OpenARDF/SignalSnagger/Software/AVR128DA48/SignalSnagger/src/eeprommanager.cpp

/*
 *  MIT License
 *
 *  Copyright (c) 2021 DigitalConfections
 *
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
 *  THE SOFTWARE IS PROVIDED "AS IS", WITHOUT WARRANTY OF ANY KIND, EXPRESS OR
 *  IMPLIED, INCLUDING BUT NOT LIMITED TO THE WARRANTIES OF MERCHANTABILITY,
 *  FITNESS FOR A PARTICULAR PURPOSE AND NONINFRINGEMENT. IN NO EVENT SHALL THE
 *  AUTHORS OR COPYRIGHT HOLDERS BE LIABLE FOR ANY CLAIM, DAMAGES OR OTHER
 *  LIABILITY, WHETHER IN AN ACTION OF CONTRACT, TORT OR OTHERWISE, ARISING FROM,
 *  OUT OF OR IN CONNECTION WITH THE SOFTWARE OR THE USE OR OTHER DEALINGS IN THE
 *  SOFTWARE.
 */

#include "defs.h"
#include "eeprommanager.h"
#include "i2c.h"
#include "receiver.h"
#include <avr/pgmspace.h>
#include <string.h>

#ifdef ATMEL_STUDIO_7
#include <avr/pgmspace.h>
#include <stdio.h>
#include <string.h>
#include <math.h>
#endif  /* ATMEL_STUDIO_7 */

/***********************************************************************
 * Global Variables & String Constants
 *
 * Identify each global with a "g_" prefix
 * Whenever possible limit globals' scope to this file using "static"
 * Use "volatile" for globals shared between ISRs and foreground loop
 ************************************************************************/

const struct EE_prom EEMEM EepromManager::ee_vars
=
{
	0x00, // 	uint16_t eeprom_initialization_flag; 
	0x00000000, // 	Guard
	0x00000000, // 	time_t event_start_epoch;
	0x00000000, // 	Guard
	0x00000000, //  time_t event_finish_epoch; 
	0x00000000, // 	Guard
	"\0\0\0\0\0\0\0\0\0\0\0\0\0\0\0\0\0\0\0\0\0", // 	char pattern_text[MAX_PATTERN_TEXT_LENGTH + 2]; 
	0x00000000, // 	Guard
	"\0\0\0\0\0\0\0\0\0\0\0\0\0\0\0\0\0\0\0\0\0", // 	char foxoring_pattern_text[MAX_PATTERN_TEXT_LENGTH + 2];
	0x00000000, // 	Guard
	"\0\0\0\0\0\0\0\0\0\0\0\0\0\0\0\0\0\0\0\0\0",  // char stationID_text[MAX_PATTERN_TEXT_LENGTH + 2];
	0x00000000, // 	Guard
	"\0\0\0\0\0\0\0\0\0", // 	uint8_t unlockCode[MAX_UNLOCK_CODE_LENGTH + 2]; 
	0x00000000, // 	Guard
	(Fox_t)0x00, // Fox_t fox_setting_none;
	0x00000000, // 	Guard
	(Fox_t)0x00, // Fox_t fox_setting_classic;
	0x00000000, // 	Guard
	(Fox_t)0x00, // Fox_t fox_setting_sprint;
	0x00000000, // 	Guard
	(Fox_t)0x00, // Fox_t fox_setting_foxoring;
	0x00000000, // 	Guard
	(Fox_t)0x00, // Fox_t fox_setting_blind;
	0x00000000, // 	Guard
	0x00, // 	uint8_t utc_offset; 
	0x00000000, // 	Guard
	0x00000000, // 	uint32_t rtty_offset; 
	0x00000000, // 	Guard
	0x0000, // 	uint16_t rf_power; 
	0x00000000, // 	Guard
	0x00, // 	uint8_t id_codespeed;
	0x00000000, // 	Guard
	0x00, // 	uint8_t pattern_codespeed;
	0x00000000, // 	Guard
	0x00, // 	uint8_t foxoring_pattern_codespeed;
	0x00000000, // 	Guard
	0x0000, // 	int16_t off_air_seconds; 
	0x00000000, // 	Guard
	0x0000, // 	int16_t on_air_seconds; 
	0x00000000, // 	Guard
	0x0000, // 	int16_t ID_period_seconds; 
	0x00000000, // 	Guard
	0x0000, // 	int16_t intra_cycle_delay_time; 
	0x00000000, // 	Guard
	(Event_t)0x00, // Event_t event_setting;
	0x00000000, // 	Guard
	0x00000000,  // uint32_t frequency;
	0x00000000, // 	Guard
	0x00000000,  // uint32_t frequency_low;
	0x00000000, // 	Guard
	0x00000000,	//	uint32_t frequency_med; 
	0x00000000, // 	Guard
	0x00000000,	// uint32_t frequency_hi;
	0x00000000,	// 	Guard
	0x00000000,	// uint32_t frequency_beacon;
	0x00000000,	// 	Guard
	0x00,		// 	uint8_t master_setting;
	0x00000000, // 	Guard
	0x00000000, //  float voltage_threshold
	0x00000000, // 	Guard
	0x0000,		//  uint16_t clock_calibration
	0x00000000, //  Guard
	0x00,       //  uint8_t days_to_run
	0x00000000, //  Guard
	0x0000,     // uint16_t i2c_failure_count;
	(Frequency_Hz)0x00000000, // Frequency_Memory
	(Frequency_Hz)0x00000000,
	(Frequency_Hz)0x00000000,
	(Frequency_Hz)0x00000000,
	(Frequency_Hz)0x00000000,
	(Frequency_Hz)0x00000000,
	(Frequency_Hz)0x00000000,
	(Frequency_Hz)0x00000000,
	(Frequency_Hz)0x00000000,
	(Frequency_Hz)0x00000000,
	(Frequency_Hz)0x00000000,
	(Frequency_Hz)0x00000000,
	(Frequency_Hz)0x00000000,
	(Frequency_Hz)0x00000000,
	(Frequency_Hz)0x00000000,
	(Frequency_Hz)0x00000000,
	(Frequency_Hz)0x00000000,
	(Frequency_Hz)0x00000000,
	(Frequency_Hz)0x00000000,
	(Frequency_Hz)0x00000000,
	0x00,       //  uint8_t channel name index
	0x00,       //  uint8_t channel name index
	0x00,       //  uint8_t channel name index
	0x00,       //  uint8_t channel name index
	0x00,       //  uint8_t channel name index
	0x00,       //  uint8_t channel name index
	0x00,       //  uint8_t channel name index
	0x00,       //  uint8_t channel name index
	0x00,       //  uint8_t channel name index
	0x00,       //  uint8_t channel name index
	0x00,       //  uint8_t channel name index
	0x00,       //  uint8_t channel name index
	0x00,       //  uint8_t channel name index
	0x00,       //  uint8_t channel name index
	0x00,       //  uint8_t channel name index
	0x00,       //  uint8_t channel name index
	0x00,       //  uint8_t channel name index
	0x00,       //  uint8_t channel name index
	0x00,       //  uint8_t channel name index
	0x00,       //  uint8_t channel name index
	(FrequencyMode_t)0x00,		//  uint8_t frequency_mode
	(BatteryCapacity_t)0x00,       //  uint8_t battery_capacity
	0x00,       //  uint8_t battery_threshold
	0x00		// uint8_t active_memory
};

bool g_isMaster = UNUSED_VAR;
volatile Fox_t g_fox[EVENT_NUMBER_OF_EVENTS] = {FOX_1, FOX_1, SPRINT_S1, FOXORING_FOX1, INVALID_FOX}; /* none, classic, sprint, foxoring, blind */
volatile int8_t g_utc_offset;
uint8_t g_unlockCode[UNLOCK_CODE_SIZE + 2];
Frequency_Hz g_rtty_offset;

volatile Event_t g_event = EVENT_NONE; // unused
extern volatile Frequency_Hz g_rx_frequency;
extern volatile Frequency_Hz g_frequency_low;
extern volatile Frequency_Hz g_frequency_med;
extern volatile Frequency_Hz g_frequency_hi;
extern volatile Frequency_Hz g_frequency_beacon;
extern Frequency_Hz g_channel_frequency[NUMBER_OF_FREQUENCY_CHANNELS];
extern uint8_t g_channel_name[NUMBER_OF_FREQUENCY_CHANNELS];
volatile FrequencyMode_t g_frequency_mode = MODE_VFO;
volatile BatteryCapacity_t g_battery_capacity = MAH_450mAh;
volatile BatteryWarnThreshold_t g_battery_warning_threshold = 10;
volatile uint8_t g_active_memory = 0;

char g_messages_text[STATION_ID+1][MAX_PATTERN_TEXT_LENGTH + 1];
volatile time_t g_event_start_epoch;
volatile time_t g_event_finish_epoch;
uint16_t g_80m_power_level_mW;
volatile uint8_t g_id_codespeed;
volatile uint8_t g_pattern_codespeed;
volatile uint8_t g_foxoring_pattern_codespeed;
volatile int16_t g_off_air_seconds;
volatile int16_t g_on_air_seconds;
volatile int16_t g_ID_period_seconds;
volatile int16_t g_intra_cycle_delay_time;
volatile float g_voltage_threshold = UNUSED_VAR;
extern uint16_t g_clock_calibration;
volatile uint8_t g_days_to_run = UNUSED_VAR;
uint16_t g_i2c_failure_count = UNUSED_VAR;
#define MAX_TX_POWER_80M_MW 5000U
#define EEPROM_RTTY_OFFSET_FREQUENCY_DEFAULT 70
#define EEPROM_TX_80M_POWER_MW_DEFAULT 3000


extern char g_tempStr[];

/* default constructor */
EepromManager::EepromManager()
{
}   /*EepromManager */

/* default destructor */
EepromManager::~EepromManager()
{
}   /*~EepromManager */

#include <inttypes.h>
#include <avr/eeprom.h>
#include <avr/io.h>

typedef uint16_t eeprom_addr_t;

// to write
void avr_eeprom_write_byte(eeprom_addr_t index, uint8_t in) {
	while (NVMCTRL.STATUS & NVMCTRL_EEBUSY_bm);
	_PROTECTED_WRITE_SPM(NVMCTRL.CTRLA, NVMCTRL_CMD_EEERWR_gc);
	*(uint8_t*)(eeprom_addr_t)(MAPPED_EEPROM_START+index) = in;
	_PROTECTED_WRITE_SPM(NVMCTRL.CTRLA, NVMCTRL_CMD_NONE_gc);
}

void avr_eeprom_write_word(eeprom_addr_t index, uint16_t in) {
	while (NVMCTRL.STATUS & NVMCTRL_EEBUSY_bm);
	_PROTECTED_WRITE_SPM(NVMCTRL.CTRLA, NVMCTRL_CMD_EEERWR_gc);
	*(uint16_t*)(eeprom_addr_t)(MAPPED_EEPROM_START+index) = in;
	_PROTECTED_WRITE_SPM(NVMCTRL.CTRLA, NVMCTRL_CMD_NONE_gc);
}

void avr_eeprom_write_dword(eeprom_addr_t index, uint32_t in) {
	while (NVMCTRL.STATUS & NVMCTRL_EEBUSY_bm);
	_PROTECTED_WRITE_SPM(NVMCTRL.CTRLA, NVMCTRL_CMD_EEERWR_gc);
	*(uint32_t*)(eeprom_addr_t)(MAPPED_EEPROM_START+index) = in;
	_PROTECTED_WRITE_SPM(NVMCTRL.CTRLA, NVMCTRL_CMD_NONE_gc);
}

void avr_eeprom_write_float(eeprom_addr_t index, float in) {
	while (NVMCTRL.STATUS & NVMCTRL_EEBUSY_bm);
	_PROTECTED_WRITE_SPM(NVMCTRL.CTRLA, NVMCTRL_CMD_EEERWR_gc);
	*(float*)(eeprom_addr_t)(MAPPED_EEPROM_START+index) = in;
	_PROTECTED_WRITE_SPM(NVMCTRL.CTRLA, NVMCTRL_CMD_NONE_gc);
}


void EepromManager::updateEEPROMVar(EE_var_t v, void* val)
{
	if(!val)
	{
		return;
	}

	switch(v)
	{
		case RTTY_offset:
		{
			if(*(uint32_t*)val != eeprom_read_dword(&(EepromManager::ee_vars.rtty_offset)))
			{
				avr_eeprom_write_dword(RTTY_offset, *(uint32_t*)val);
			}
		}
		break;
		
		case RF_Power:
		{
			if(*(uint16_t*)val != eeprom_read_word(&(EepromManager::ee_vars.rf_power)))
			{
				avr_eeprom_write_word(RF_Power, *(uint16_t*)val);
			}			
		}
		break;
		
		case StationID_text:
		{
			int cnt = 0;
			char* char_addr = (char*)val;
			char c = *char_addr++;
			char q;
			
			eeprom_addr_t j = (eeprom_addr_t)StationID_text;

			while(c && (cnt<MAX_PATTERN_TEXT_LENGTH))
			{
				q = (char)eeprom_read_byte((uint8_t*)j);
				if(c != q)
				{
					avr_eeprom_write_byte(j, c);
				}
				
				cnt++;
				c = *char_addr++;
				j++;
			}

			avr_eeprom_write_byte(j, 0);
		}
		break;

		case Pattern_text:
		{
			int cnt = 0;
			char* char_addr = (char*)val;
			char c = *char_addr++;
			char q;
			
			eeprom_addr_t j = (eeprom_addr_t)Pattern_text;

			while(c && (cnt<MAX_PATTERN_TEXT_LENGTH))
			{
				q = (char)eeprom_read_byte((uint8_t*)j);
				if(c != q)
				{
					avr_eeprom_write_byte(j, c);
				}
				
				cnt++;
				c = *char_addr++;
				j++;
			}

			avr_eeprom_write_byte(j, 0);
		}
		break;
				
		case Foxoring_pattern_text:
		{
			int cnt = 0;
			char* char_addr = (char*)val;
			char c = *char_addr++;
			char q;
			
			eeprom_addr_t j = (eeprom_addr_t)Foxoring_pattern_text;

			while(c && (cnt<MAX_PATTERN_TEXT_LENGTH))
			{
				q = (char)eeprom_read_byte((uint8_t*)j);
				if(c != q)
				{
					avr_eeprom_write_byte(j, c);
				}
				
				cnt++;
				c = *char_addr++;
				j++;
			}

			avr_eeprom_write_byte(j, 0);
		}
		break;

		case UnlockCode:
		{
			int cnt = 0;
			char* char_addr = (char*)val;
			char c = *char_addr++;
			char q;
			
			eeprom_addr_t j = (eeprom_addr_t)UnlockCode;

			while(c && (cnt<MAX_UNLOCK_CODE_LENGTH))
			{
				q = (char)eeprom_read_byte((uint8_t*)j);
				if(c != q)
				{
					avr_eeprom_write_byte(j, c);
				}
				
				cnt++;
				j++;
				c = *char_addr++;
			}

			avr_eeprom_write_byte(j, 0);
		}
		break;

		case Id_codespeed:
		{
			if(*(uint8_t*)val != eeprom_read_byte(&(EepromManager::ee_vars.id_codespeed)))
			{
				avr_eeprom_write_byte(Id_codespeed, *(uint8_t*)val);
			}
		}
		break;
		
		case Pattern_Code_Speed:
		{
			if(*(uint8_t*)val != eeprom_read_byte(&(EepromManager::ee_vars.pattern_codespeed)))
			{
				avr_eeprom_write_byte(Pattern_Code_Speed, *(uint8_t*)val);
			}
		}
		break;
		
		case Foxoring_Pattern_Code_Speed:
		{
			if(*(uint8_t*)val != eeprom_read_byte(&(EepromManager::ee_vars.foxoring_pattern_codespeed)))
			{
				avr_eeprom_write_byte(Foxoring_Pattern_Code_Speed, *(uint8_t*)val);
			}
		}
		break;

		case Fox_setting_none:
		{
			if(*(uint8_t*)val != eeprom_read_byte((uint8_t*)&(EepromManager::ee_vars.fox_setting_none)))
			{
				avr_eeprom_write_byte(Fox_setting_none, *(uint8_t*)val);
			}
		}
		break;
		
		case Fox_setting_classic:
		{
			if(*(uint8_t*)val != eeprom_read_byte((uint8_t*)&(EepromManager::ee_vars.fox_setting_classic)))
			{
				avr_eeprom_write_byte(Fox_setting_classic, *(uint8_t*)val);
			}
		}
		break;
		
		case Fox_setting_sprint:
		{
			if(*(uint8_t*)val != eeprom_read_byte((uint8_t*)&(EepromManager::ee_vars.fox_setting_sprint)))
			{
				avr_eeprom_write_byte(Fox_setting_sprint, *(uint8_t*)val);
			}
		}
		break;
		
		case Fox_setting_foxoring:
		{
			if(*(uint8_t*)val != eeprom_read_byte((uint8_t*)&(EepromManager::ee_vars.fox_setting_foxoring)))
			{
				avr_eeprom_write_byte(Fox_setting_foxoring, *(uint8_t*)val);
			}
		}
		break;
		
		case Fox_setting_blind:
		{
			if(*(uint8_t*)val != eeprom_read_byte((uint8_t*)&(EepromManager::ee_vars.fox_setting_blind)))
			{
				avr_eeprom_write_byte(Fox_setting_blind, *(uint8_t*)val);
			}			
		}
		break;
		
		case Master_setting:
		{
			if(*(uint8_t*)val != eeprom_read_byte((uint8_t*)&(EepromManager::ee_vars.master_setting)))
			{
				avr_eeprom_write_byte(Master_setting, *(uint8_t*)val);
			}
		}
		break;
		
		case Event_setting:
		{
			if(*(uint8_t*)val != eeprom_read_byte((uint8_t*)&(EepromManager::ee_vars.event_setting)))
			{
				avr_eeprom_write_byte(Event_setting, *(uint8_t*)val);
			}
		}
		break;
		
		case Frequency:
		{
			if(*(uint32_t*)val != eeprom_read_dword(&(EepromManager::ee_vars.frequency)))
			{
				avr_eeprom_write_dword(Frequency, *(uint32_t*)val);
			}
		}
		break;
		
		case Frequency_Low:
		{
			if(*(uint32_t*)val != eeprom_read_dword(&(EepromManager::ee_vars.frequency_low)))
			{
				avr_eeprom_write_dword(Frequency_Low, *(uint32_t*)val);
			}
		}
		break;
		
		case Frequency_Med:
		{
			if(*(uint32_t*)val != eeprom_read_dword(&(EepromManager::ee_vars.frequency_med)))
			{
				avr_eeprom_write_dword(Frequency_Med, *(uint32_t*)val);
			}
		}
		break;
		
		case Frequency_Hi:
		{
			if(*(uint32_t*)val != eeprom_read_dword(&(EepromManager::ee_vars.frequency_high)))
			{
				avr_eeprom_write_dword(Frequency_Hi, *(uint32_t*)val);
			}
		}
		break;
		
		case Frequency_Beacon:
		{
			if(*(uint32_t*)val != eeprom_read_dword(&(EepromManager::ee_vars.frequency_beacon)))
			{
				avr_eeprom_write_dword(Frequency_Beacon, *(uint32_t*)val);
			}
		}
		break;

		case Event_start_epoch:
		{
			if(*(uint32_t*)val != eeprom_read_dword(&(EepromManager::ee_vars.event_start_epoch)))
			{
				avr_eeprom_write_dword(Event_start_epoch, *(uint32_t*)val);
			}
		}
		break;

		case Event_finish_epoch:
		{
			if(*(uint32_t*)val != eeprom_read_dword(&(EepromManager::ee_vars.event_finish_epoch)))
			{
				avr_eeprom_write_dword(Event_finish_epoch, *(uint32_t*)val);
			}		
		}
		break;

		case Utc_offset:
		{
			if(*(uint8_t*)val != eeprom_read_byte(&(EepromManager::ee_vars.utc_offset)))
			{
				avr_eeprom_write_byte(Utc_offset, *(uint8_t*)val);
			}		
		}
		break;
		
		case Off_Air_Seconds:
		{
			if(*(int16_t*)val != (int16_t)eeprom_read_word((const uint16_t *)&(EepromManager::ee_vars.off_air_seconds)))
			{
				avr_eeprom_write_word(Off_Air_Seconds, *(uint16_t*)val);
			}
		}
		break;
		
		case On_Air_Seconds:
		{
			if(*(int16_t*)val != (int16_t)eeprom_read_word((const uint16_t *)&(EepromManager::ee_vars.on_air_seconds)))
			{
				avr_eeprom_write_word(On_Air_Seconds, *(uint16_t*)val);
			}
		}
		break;
		
		case ID_Period_Seconds:
		{
			if(*(int16_t*)val != (int16_t)eeprom_read_word((const uint16_t *)&(EepromManager::ee_vars.ID_period_seconds)))
			{
				avr_eeprom_write_word(ID_Period_Seconds, *(uint16_t*)val);
			}
		}
		break;
		
		case Intra_Cycle_Delay_Seconds:
		{
			if(*(int16_t*)val != (int16_t)eeprom_read_word((const uint16_t *)&(EepromManager::ee_vars.intra_cycle_delay_time)))
			{
				avr_eeprom_write_word(Intra_Cycle_Delay_Seconds, *(uint16_t*)val);
			}		
		}
		break;

		case Eeprom_initialization_flag:
		{
			if(*(int16_t*)val != (int16_t)eeprom_read_word((const uint16_t *)&(EepromManager::ee_vars.eeprom_initialization_flag)))
			{
				avr_eeprom_write_word(Eeprom_initialization_flag, *(uint16_t*)val);
			}		
		}
		break;
		
		case Voltage_threshold:
		{
			if(*(float*)val != eeprom_read_float(&(EepromManager::ee_vars.voltage_threshold)))
			{
				avr_eeprom_write_float(Voltage_threshold, *(float*)val);
			}
		}
		break;
		
		case Clock_calibration:
		{
			if(*(uint16_t*)val != eeprom_read_word(&(EepromManager::ee_vars.clock_calibration)))
			{
				avr_eeprom_write_word(Clock_calibration, *(uint16_t*)val);
			}
		}
		break;
		
		
		case Days_to_run:
		{
			if(*(uint8_t*)val != eeprom_read_byte(&(EepromManager::ee_vars.days_to_run)))
			{
				avr_eeprom_write_byte(Days_to_run, *(uint8_t*)val);
			}
		}
		break;
		
		
		case I2C_failure_count:
		{
			if(*(uint16_t*)val != eeprom_read_word(&(EepromManager::ee_vars.i2c_failure_count)))
			{
				avr_eeprom_write_byte(I2C_failure_count, *(uint8_t*)val);
			}
		}
		break;
		
		
		case Frequency_Memory:
		{
			int cnt = 0;
			Frequency_Hz* freq_addr = (Frequency_Hz*)val;
			Frequency_Hz f = *freq_addr;
			Frequency_Hz q;
			
			eeprom_addr_t j = (eeprom_addr_t)Frequency_Memory;

			while(cnt<NUMBER_OF_FREQUENCY_CHANNELS)
			{
				q = (Frequency_Hz)eeprom_read_dword((uint32_t*)j);
				if(f != q)
				{
					avr_eeprom_write_dword(j, f);
				}

				cnt++;
				freq_addr++;
				f = *freq_addr;
				j += 4;
			}
		}
		break;
		
		
		case Channel_Name:
		{
			int cnt = 0;
			uint8_t* name_addr = (uint8_t*)val;
			uint8_t n = *name_addr;
			uint8_t q;
			
			eeprom_addr_t j = (eeprom_addr_t)Channel_Name;

			while(cnt<NUMBER_OF_FREQUENCY_CHANNELS)
			{
				q = (uint8_t)eeprom_read_byte((uint8_t*)j);
				if(n != q)
				{
					avr_eeprom_write_dword(j, n);
				}

				cnt++;
				name_addr++;
				n = *name_addr;
				j++;
			}
		}
		break;
		
		
		case Frequency_Mode:
		{
			if(*(uint8_t*)val != eeprom_read_byte((uint8_t*)&(EepromManager::ee_vars.frequency_mode)))
			{
				avr_eeprom_write_byte(Frequency_Mode, *(uint8_t*)val);
			}
		}
		break;
		
		
		case Battery_Capacity:
		{
			if(*(uint8_t*)val != eeprom_read_byte((uint8_t*)&(EepromManager::ee_vars.battery_capacity)))
			{
				avr_eeprom_write_byte(Battery_Capacity, *(uint8_t*)val);
			}
		}
		break;
		
		
		case Battery_Threshold:
		{
			if(*(uint8_t*)val != eeprom_read_byte((uint8_t*)&(EepromManager::ee_vars.battery_threshold)))
			{
				avr_eeprom_write_byte(Battery_Threshold, *(uint8_t*)val);
			}
		}
		break;
		
		
		case Active_Memory:
		{
			if(*(uint8_t*)val != eeprom_read_byte((uint8_t*)&(EepromManager::ee_vars.active_memory)))
			{
				avr_eeprom_write_byte(Active_Memory, *(uint8_t*)val);
			}
		}
		break;

		default:
		{

		}
		break;
	}
}

/** 
 * Store any changed EEPROM variables
 */
void EepromManager::saveAllEEPROM(void)
{
	updateEEPROMVar(Id_codespeed, (void*)&g_id_codespeed);	
	updateEEPROMVar(Fox_setting_none, (void*)&g_fox[EVENT_NONE]);
	updateEEPROMVar(Fox_setting_classic, (void*)&g_fox[EVENT_CLASSIC]);
	updateEEPROMVar(Fox_setting_sprint, (void*)&g_fox[EVENT_SPRINT]);
	updateEEPROMVar(Fox_setting_foxoring, (void*)&g_fox[EVENT_FOXORING]);
	updateEEPROMVar(Fox_setting_blind, (void*)&g_fox[EVENT_BLIND_ARDF]);
	updateEEPROMVar(Event_setting, (void*)&g_event);
	updateEEPROMVar(Frequency, (void*)&g_rx_frequency);
	updateEEPROMVar(Frequency_Low, (void*)&g_frequency_low);
	updateEEPROMVar(Frequency_Med, (void*)&g_frequency_med); /* use for sprint slow */
	updateEEPROMVar(Frequency_Hi, (void*)&g_frequency_hi); /* use for sprint high - will also need sprint spectator and beacon */
	updateEEPROMVar(Frequency_Beacon, (void*)&g_frequency_beacon);
	updateEEPROMVar(Event_start_epoch, (void*)&g_event_start_epoch);
	updateEEPROMVar(Event_finish_epoch, (void*)&g_event_finish_epoch);
	updateEEPROMVar(Utc_offset, (void*)&g_utc_offset);
	updateEEPROMVar(Pattern_text, (void*)g_messages_text[PATTERN_TEXT]);
	updateEEPROMVar(Foxoring_pattern_text, (void*)g_messages_text[FOXORING_PATTERN_TEXT]);
	updateEEPROMVar(StationID_text, (void*)g_messages_text[STATION_ID]);
	updateEEPROMVar(UnlockCode, (void*)g_unlockCode);
	updateEEPROMVar(RTTY_offset, (void*)&g_rtty_offset);
	updateEEPROMVar(RF_Power, (void*)&g_80m_power_level_mW);
	updateEEPROMVar(Pattern_Code_Speed, (void*)&g_pattern_codespeed);
	updateEEPROMVar(Foxoring_Pattern_Code_Speed, (void*)&g_foxoring_pattern_codespeed);
	updateEEPROMVar(Off_Air_Seconds, (void*)&g_off_air_seconds);
	updateEEPROMVar(On_Air_Seconds, (void*)&g_on_air_seconds);
	updateEEPROMVar(ID_Period_Seconds, (void*)&g_ID_period_seconds);
	updateEEPROMVar(Intra_Cycle_Delay_Seconds, (void*)&g_intra_cycle_delay_time);
	updateEEPROMVar(Voltage_threshold, (void*)&g_voltage_threshold);
	updateEEPROMVar(Clock_calibration, (void*)&g_clock_calibration);
	updateEEPROMVar(Days_to_run, (void*)&g_days_to_run);
	updateEEPROMVar(I2C_failure_count, (void*)&g_i2c_failure_count);
	updateEEPROMVar(Frequency_Memory, (void*)&g_channel_frequency[0]);
	updateEEPROMVar(Channel_Name, (void*)&g_channel_name[0]);
	updateEEPROMVar(Frequency_Mode, (void*)&g_frequency_mode);
	updateEEPROMVar(Battery_Capacity, (void*)&g_battery_capacity);
	updateEEPROMVar(Battery_Threshold, (void*)&g_battery_warning_threshold);
	updateEEPROMVar(Active_Memory, (void*)&g_active_memory);
}


bool EepromManager::readNonVols(void)
{
	bool failure = true;
	uint16_t i;
	uint16_t initialization_flag = eeprom_read_word(0);

	if(initialization_flag == EEPROM_INITIALIZED_FLAG)  /* EEPROM is up to date */
	{
		g_isMaster = EEPROM_MASTER_SETTING_DEFAULT; // (int8_t)eeprom_read_byte(&(EepromManager::ee_vars.master_setting));
		g_id_codespeed = CLAMP(MIN_CODE_SPEED_WPM, eeprom_read_byte(&(EepromManager::ee_vars.id_codespeed)), MAX_CODE_SPEED_WPM);
		g_event = (Event_t)eeprom_read_byte((const uint8_t*)&(EepromManager::ee_vars.event_setting));
		g_rx_frequency = CLAMP(RX_MINIMUM_80M_FREQUENCY, eeprom_read_dword(&(EepromManager::ee_vars.frequency)), RX_MAXIMUM_80M_FREQUENCY);
		g_frequency_low = CLAMP(RX_MINIMUM_80M_FREQUENCY, eeprom_read_dword(&(EepromManager::ee_vars.frequency_low)), RX_MAXIMUM_80M_FREQUENCY);
		g_frequency_med = CLAMP(RX_MINIMUM_80M_FREQUENCY, eeprom_read_dword(&(EepromManager::ee_vars.frequency_med)), RX_MAXIMUM_80M_FREQUENCY);
		g_frequency_hi = CLAMP(RX_MINIMUM_80M_FREQUENCY, eeprom_read_dword(&(EepromManager::ee_vars.frequency_high)), RX_MAXIMUM_80M_FREQUENCY);
		g_frequency_beacon = CLAMP(RX_MINIMUM_80M_FREQUENCY, eeprom_read_dword(&(EepromManager::ee_vars.frequency_beacon)), RX_MAXIMUM_80M_FREQUENCY);
		g_fox[EVENT_NONE] = (Fox_t)(CLAMP(BEACON, eeprom_read_byte((uint8_t*)&(EepromManager::ee_vars.fox_setting_none)), SPRINT_F5));
		g_fox[EVENT_CLASSIC] = (Fox_t)(CLAMP(BEACON, eeprom_read_byte((uint8_t*)&(EepromManager::ee_vars.fox_setting_classic)), FOX_5));
		g_fox[EVENT_SPRINT] = (Fox_t)(CLAMP(BEACON, eeprom_read_byte((uint8_t*)&(EepromManager::ee_vars.fox_setting_sprint)), SPRINT_F5));
		g_fox[EVENT_FOXORING] = (Fox_t)(CLAMP(BEACON, eeprom_read_byte((uint8_t*)&(EepromManager::ee_vars.fox_setting_foxoring)), FOXORING_FOX3));
		g_fox[EVENT_BLIND_ARDF] = (Fox_t)(CLAMP(BEACON, eeprom_read_byte((uint8_t*)&(EepromManager::ee_vars.fox_setting_blind)), FOX_5));
		g_event_start_epoch = eeprom_read_dword(&(EepromManager::ee_vars.event_start_epoch));
		g_event_finish_epoch = eeprom_read_dword(&(EepromManager::ee_vars.event_finish_epoch));
		g_utc_offset = (int8_t)eeprom_read_byte(&(EepromManager::ee_vars.utc_offset));

		char c;
		for(i = 0; i < MAX_PATTERN_TEXT_LENGTH; i++)
		{
			c = (char)eeprom_read_byte((uint8_t*)(&(EepromManager::ee_vars.pattern_text[i])));			
			if(c==255) c=0;
			g_messages_text[PATTERN_TEXT][i] = c;
			if(!c)
			{
				break;
			}
		}

		for(i = 0; i < MAX_PATTERN_TEXT_LENGTH; i++)
		{
			c = (char)eeprom_read_byte((uint8_t*)(&(EepromManager::ee_vars.foxoring_pattern_text[i])));			
			if(c==255) c=0;
			g_messages_text[FOXORING_PATTERN_TEXT][i] = c;
			if(!c)
			{
				break;
			}
		}

		for(i = 0; i < MAX_PATTERN_TEXT_LENGTH; i++)
		{
			c = (char)eeprom_read_byte((uint8_t*)(&(EepromManager::ee_vars.stationID_text[i])));
			if(c == 255) c= 0;
			g_messages_text[STATION_ID][i] = c;
			if(!c)
			{
				break;
			}
		}

		for(i = 0; i < MAX_UNLOCK_CODE_LENGTH; i++)
		{
			c = (char)eeprom_read_byte((uint8_t*)(&(EepromManager::ee_vars.unlockCode[i])));	
			if(c==255) c=0;
			g_unlockCode[i] = c;
			if(!c)
			{
				break;
			}
		}
		
		g_rtty_offset =eeprom_read_dword(&(EepromManager::ee_vars.rtty_offset));
 		g_80m_power_level_mW = CLAMP(MIN_RF_POWER_MW, (uint16_t)eeprom_read_word(&(EepromManager::ee_vars.rf_power)), MAX_TX_POWER_80M_MW);

		g_pattern_codespeed = CLAMP(MIN_CODE_SPEED_WPM, eeprom_read_byte((uint8_t*)(&(EepromManager::ee_vars.pattern_codespeed))), MAX_CODE_SPEED_WPM);
		g_foxoring_pattern_codespeed = CLAMP(MIN_CODE_SPEED_WPM, eeprom_read_byte((uint8_t*)(&(EepromManager::ee_vars.foxoring_pattern_codespeed))), MAX_CODE_SPEED_WPM);

		g_off_air_seconds = CLAMP(0, (int16_t)eeprom_read_word((const uint16_t*)&(EepromManager::ee_vars.off_air_seconds)), 3600);
		g_on_air_seconds = CLAMP(0, (int16_t)eeprom_read_word((const uint16_t*)&(EepromManager::ee_vars.on_air_seconds)), 3600);
		g_ID_period_seconds = CLAMP(0, (int16_t)eeprom_read_word((const uint16_t*)&(EepromManager::ee_vars.ID_period_seconds)), 3600);
		g_intra_cycle_delay_time = CLAMP(0, (int16_t)eeprom_read_word((const uint16_t*)&(EepromManager::ee_vars.intra_cycle_delay_time)), 3600);
		
		g_voltage_threshold = CLAMP(0.1, eeprom_read_float(&(EepromManager::ee_vars.voltage_threshold)), 15.0);
		
		g_clock_calibration = eeprom_read_word(&(EepromManager::ee_vars.clock_calibration));

		g_days_to_run = eeprom_read_byte((uint8_t*)(&(EepromManager::ee_vars.days_to_run)));
		
		g_i2c_failure_count = eeprom_read_word((uint16_t*)(&(EepromManager::ee_vars.i2c_failure_count)));
		
		Frequency_Hz f;
		for(i = 0; i < NUMBER_OF_FREQUENCY_CHANNELS; i++)
		{
			f = eeprom_read_dword(&(EepromManager::ee_vars.channel_frequency[i]));
			if(f==0xFFFFFFFF) f=0;
			if((f==0) || ((f <= RX_MAXIMUM_80M_FREQUENCY) && (f >= RX_MINIMUM_80M_FREQUENCY)))
			{
				g_channel_frequency[i] = f;
			}
		}
		
		uint8_t x;
		for(i=0; i<NUMBER_OF_FREQUENCY_CHANNELS; i++)
		{
			x = eeprom_read_byte(&(EepromManager::ee_vars.channel_name[i]));
			if(x >= NUMBER_OF_FREQUENCY_CHANNEL_NAMES) x = 0;
			g_channel_name[i] = x;
		}
		
		g_frequency_mode = (FrequencyMode_t)eeprom_read_byte((const uint8_t*)&(EepromManager::ee_vars.frequency_mode));
		if(g_frequency_mode != MODE_MEMORY) g_frequency_mode = MODE_VFO;
		
		g_battery_capacity = (BatteryCapacity_t)eeprom_read_byte((uint8_t*)&(EepromManager::ee_vars.battery_capacity));
		if((uint8_t)g_battery_capacity > NUMBER_OF_BATTERY_CAPACITY_VALUES) g_battery_capacity = MAH_450mAh;
		
		g_battery_warning_threshold = (BatteryWarnThreshold_t)eeprom_read_byte((uint8_t*)&(EepromManager::ee_vars.battery_threshold));
		if((uint8_t)g_battery_warning_threshold > 100) g_battery_warning_threshold = 10;
		
		g_active_memory = (uint8_t)eeprom_read_byte((uint8_t*)&(EepromManager::ee_vars.active_memory));
		if((uint8_t)g_active_memory > NUMBER_OF_FREQUENCY_CHANNELS) g_active_memory = 0;

		failure = false;
	}

	return(failure);
}

/*
 * Set volatile variables to their values stored in EEPROM
 */
	bool EepromManager::initializeEEPROMVars(void)
	{
		bool err = false;
		uint16_t i, j;

		uint16_t initialization_flag = eeprom_read_word(0);

		if(initialization_flag != EEPROM_INITIALIZED_FLAG)
		{
			g_id_codespeed = EEPROM_ID_CODE_SPEED_DEFAULT;
			avr_eeprom_write_byte(Id_codespeed, g_id_codespeed);
			
			g_isMaster = EEPROM_MASTER_SETTING_DEFAULT;
			avr_eeprom_write_byte(Master_setting, g_isMaster);

			g_fox[EVENT_NONE] = EEPROM_FOX_SETTING_NONE_DEFAULT;
			avr_eeprom_write_byte(Fox_setting_none, (uint8_t)g_fox[EVENT_NONE]);
			
			g_fox[EVENT_CLASSIC] = EEPROM_FOX_SETTING_CLASSIC_DEFAULT;
			avr_eeprom_write_byte(Fox_setting_classic, (uint8_t)g_fox[EVENT_CLASSIC]);
			
			g_fox[EVENT_SPRINT] = EEPROM_FOX_SETTING_SPRINT_DEFAULT;
			avr_eeprom_write_byte(Fox_setting_sprint, (uint8_t)g_fox[EVENT_SPRINT]);
			
			g_fox[EVENT_FOXORING] = EEPROM_FOX_SETTING_FOXORING_DEFAULT;
			avr_eeprom_write_byte(Fox_setting_foxoring, (uint8_t)g_fox[EVENT_FOXORING]);
			
			g_fox[EVENT_BLIND_ARDF] = EEPROM_FOX_SETTING_BLIND_DEFAULT;
			avr_eeprom_write_byte(Fox_setting_blind, (uint8_t)g_fox[EVENT_BLIND_ARDF]);
			
			g_event = EEPROM_EVENT_SETTING_DEFAULT;
			avr_eeprom_write_byte(Event_setting, (uint8_t)g_event);
			
			g_rx_frequency = EEPROM_FREQUENCY_DEFAULT;
			avr_eeprom_write_dword(Frequency, g_rx_frequency);
			
			g_frequency_low = EEPROM_FREQUENCY_LOW_DEFAULT;
			avr_eeprom_write_dword(Frequency_Low, g_frequency_low);
			
			g_frequency_med = EEPROM_FREQUENCY_MED_DEFAULT;
			avr_eeprom_write_dword(Frequency_Med, g_frequency_med);
			
			g_frequency_hi = EEPROM_FREQUENCY_HI_DEFAULT;
			avr_eeprom_write_dword(Frequency_Hi, g_frequency_hi);
			
			g_frequency_beacon = EEPROM_FREQUENCY_BEACON_DEFAULT;
			avr_eeprom_write_dword(Frequency_Beacon, g_frequency_beacon);

			g_event_start_epoch = EEPROM_START_EPOCH_DEFAULT;
			avr_eeprom_write_dword(Event_start_epoch, g_event_start_epoch);

			g_event_finish_epoch = EEPROM_FINISH_EPOCH_DEFAULT;
			avr_eeprom_write_dword(Event_finish_epoch, g_event_finish_epoch);

			g_utc_offset = EEPROM_UTC_OFFSET_DEFAULT;
			avr_eeprom_write_byte(Utc_offset, (uint8_t)g_utc_offset);

			g_messages_text[STATION_ID][0] = '\0';
			avr_eeprom_write_byte(StationID_text, 0);

			uint8_t *v = (uint8_t*)EEPROM_FOX_PATTERN_DEFAULT;
			i = Pattern_text;
			for(j = 0; j < strlen(EEPROM_FOX_PATTERN_DEFAULT); j++)
			{
				g_messages_text[PATTERN_TEXT][j] = *v;
				avr_eeprom_write_byte(i++, *v++);
			}
			
			avr_eeprom_write_byte(i, '\0');

			v = (uint8_t*)EEPROM_FOXORING_PATTERN_DEFAULT;
			i = Foxoring_pattern_text;
			for(j = 0; j < strlen(EEPROM_FOXORING_PATTERN_DEFAULT); j++)
			{
				g_messages_text[FOXORING_PATTERN_TEXT][j] = *v;
				avr_eeprom_write_byte(i++, *v++);
			}
			
			avr_eeprom_write_byte(i, '\0');

			v = (uint8_t*)EEPROM_DTMF_UNLOCK_CODE_DEFAULT;
			i = UnlockCode;
			for(j = 0; j < strlen(EEPROM_DTMF_UNLOCK_CODE_DEFAULT); j++)
			{
				g_unlockCode[j] = *v;
				avr_eeprom_write_byte(i++, *v++);
			}

			avr_eeprom_write_byte(i, '\0');
			g_unlockCode[j] = '\0';
			
			g_rtty_offset = EEPROM_RTTY_OFFSET_FREQUENCY_DEFAULT;
			avr_eeprom_write_dword(RTTY_offset, g_rtty_offset);

			g_80m_power_level_mW = EEPROM_TX_80M_POWER_MW_DEFAULT;
			avr_eeprom_write_dword(RF_Power, g_80m_power_level_mW);
			
			g_pattern_codespeed = EEPROM_PATTERN_CODE_SPEED_DEFAULT;
			avr_eeprom_write_byte(Pattern_Code_Speed, g_pattern_codespeed);
			
			g_foxoring_pattern_codespeed = EEPROM_FOXORING_PATTERN_CODESPEED_DEFAULT;
			avr_eeprom_write_byte(Foxoring_Pattern_Code_Speed, g_foxoring_pattern_codespeed);
			
			g_off_air_seconds = EEPROM_OFF_AIR_TIME_DEFAULT;
			avr_eeprom_write_word(Off_Air_Seconds, g_off_air_seconds);
			
			g_on_air_seconds = EEPROM_ON_AIR_TIME_DEFAULT;
			avr_eeprom_write_word(On_Air_Seconds, g_on_air_seconds);
		
			g_ID_period_seconds = EEPROM_ID_TIME_INTERVAL_DEFAULT;
			avr_eeprom_write_word(ID_Period_Seconds, g_ID_period_seconds);
			
			g_intra_cycle_delay_time = EEPROM_INTRA_CYCLE_DELAY_TIME_DEFAULT;
			avr_eeprom_write_word(Intra_Cycle_Delay_Seconds, g_intra_cycle_delay_time);

			avr_eeprom_write_byte(i, '\0');

			g_voltage_threshold = EEPROM_BATTERY_THRESHOLD_V;
			avr_eeprom_write_float(Voltage_threshold, g_voltage_threshold);
			
			g_clock_calibration = EEPROM_CLOCK_CALIBRATION_DEFAULT;
			avr_eeprom_write_word(Clock_calibration, g_clock_calibration);

			g_days_to_run = 1;
			avr_eeprom_write_byte(Days_to_run, g_days_to_run);
			
			g_i2c_failure_count = 0;
			avr_eeprom_write_dword(I2C_failure_count, g_i2c_failure_count);

			i = Frequency_Memory;
			for(j = 0; j < NUMBER_OF_FREQUENCY_CHANNELS; j++)
			{
				g_channel_frequency[j] = 0;
				avr_eeprom_write_dword(i, 0);
				i += 4;
			}
			
			i = Channel_Name;
			for(j=0; j<NUMBER_OF_FREQUENCY_CHANNELS; j++)
			{
				g_channel_name[j] = 0;
				avr_eeprom_write_byte(i++, 0);
			}
			
			g_frequency_mode = MODE_VFO;
			avr_eeprom_write_byte(Frequency_Mode, g_frequency_mode);
			
			g_battery_capacity = MAH_450mAh;
			avr_eeprom_write_byte(Battery_Capacity, g_battery_capacity);
			
			g_battery_warning_threshold = 10;
			avr_eeprom_write_byte(Battery_Threshold, g_battery_warning_threshold);
			
			/* Done */

			avr_eeprom_write_word(0, EEPROM_INITIALIZED_FLAG);
		}
		
		return(err);
	}
