OpenARDF/SignalSnagger/Software/AVR128DA48/SignalSnagger/include/si5351.h

/*
 *  MIT License
 *
 *  Copyright (c) 2022 DigitalConfections
 *
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
 * The Si5351 is an I2C configurable clock generator that is ideally suited for replacing crystals,
 * crystal oscillators, VCXOs, phase-locked loops (PLLs), and fanout buffers in cost-sensitive
 * applications. Based on a PLL/VCXO + high resolution MultiSynth fractional divider architecture,
 * the Si5351 can generate any frequency up to 200 MHz on each of its outputs with 0 ppm error.
 * http://www.silabs.com/documents/public/data-sheets/Si5351-B.pdf
 *
 * PURPOSE
 * This is a basic library for the Si5351 series of clock generator ICs from Silicon Labs for the avr-gcc development
 * environment. It supports controlling the Si5351 with an AVR microcontroller with a TWI peripheral module. It is
 * intentionally minimalistic in order to minimize program size and maximize execution speed. It is intended for use
 * in projects utilizing small processors with limited program memory, where the program author is responsible for
 * implementing any checks on the validity of parameters passed to the library functions.
 *
 * The following high-level description of the Si5351 frequency-setting algorithm is provided to help the user understand
 * the basic workings of the library, so that any needed modifications can be readily made.
 *
 * OVERVIEW
 * The algorithm used in this library starts with the desired output frequency, and works backwards through Synthesis
 * Stage 2 and Synthesis Stage 1, to determine the necessary Si5351 register settings.
 *
 * STEPS (Output CLK0)
 *
 * 1. Choose a desired CLK0 output frequency (Fout) in Hz.
 * 2. Find an even integer Multisynth Divider Ratio (a_msd) that multiplies Fout to obtain a value between 600 MHz and 900 MHz. Set b_msd = 0,
 *    and c_msd = 1. Note: a_msd has a valid range of all even integers between 4 and 900; we are choosing to exclude all odd and fractional solutions.
 * 3. Calculate the VCO frequency (Fvco) in Hz where Fvco = a_msd x Fout.
 * 4. Find values for the Feedback Multisynth Divider Equation (a_fmd, b_fmd, c_fmd) that will multiply the crystal oscillator frequency (Fxtal)
 *    to obtain Fvco = Fxtal x (a_fmd + (b_fmd/c_fmd)). Note: (a_fmd + (b_fmd/c_fmd)) has a valid range of 15 to 90 with resolution of 1/1048575.
 * 5. Apply settings derived in previous steps to program PLLA, and use PLLA to generate Fout on CLK0.
 *
 *
 * STEPS (Output CLK1)
 *
 * CLK1 steps are exactly the same as for CLK0, except for Step 5, where we will program PLLB, and use PLLB to generate Fout on CLK1.
 *
 *
 * STEPS (Output CLK2)
 *
 * 1. Choose a desired CLK2 output frequency (Fout) in Hz.
 * 2. Starting with the Fvco applied to PLLB to generate CLK1, derive a Multisynth Divider Ratio (a_msd, b_msd and c_msd) that multiplies
 *    Fvco to obtain Fout = Fvco x (a_msd + (b_msd/c_msd)). Note: (a_msd + (b_msd/c_msd)) has a valid range of 4, 6, and all values between
 *    8 and 900 with resolution of 1/1048575. The resulting Fout might not be exact.
 * 3. Apply settings derived in Step 2 to use PLLB to generate Fout on CLK2.
 *
 * NOTE:
 * The order of setting clocks CLK1 and CLK2 may be reversed. If that is done, then the Fvco for PLLB will be derived from the Fout chosen
 * for CLK2 (instead of CLK1 as shown in the steps above). Thus the order in which clocks CLK1 and CLK2 are set, can affect Fvco for PLLB,
 * and therefore the accuracy of the clock settings. However, if the PLLB VCO frequency is first set (using si5351_set_vcoB_freq())
 * then both CLK1 and CLK2 will use the specified VCO frequency to derive the signals on those outputs.
 *
 */

#include "defs.h"

#ifndef SI5351_H_
#define SI5351_H_

//#include <avr/eeprom.h>

#ifdef __cplusplus
extern "C" {
#endif


/********************************************************************************************************************
 *  Notes:
 *      Only one hardware version of the Si5351 device is supported by this library:
 *          Si5351A MSOP10 (3 output clocks, XTAL input)
 *          PLL usage is as follows, change code to modify this behavior:
 *              CLK0 uses PLLA,
 *              CLK1 uses PLLB
 *              CLK2 uses PLLB
 *
 *
 *  CODE EXAMPLES:
 *
 *     Example 1: Set CLK0 to 144.571 MHz
 *        si5351_init(SI5351_CRYSTAL_LOAD_10PF, 0);
 *        si5351_set_freq(144571000, SI5351_CLK0);
 *
 *     Example 2: Set CLK0 to 133.3 MHz, then use PLL VCO of 700 MHz to set CLK2 to 70MHz, and CLK1 to 10.705 MHz
 *        si5351_init(SI5351_CRYSTAL_LOAD_10PF, 0);
 *        si5351_set_freq(133300000, SI5351_CLK0);
 *        si5351_set_vcoB_freq(700000000);
 *        si5351_set_freq(70000000, SI5351_CLK2);
 *        si5351_set_freq(10705000, SI5351_CLK1);
 *
 *  The Si5351 needs only to be initialized once at power up. Initialization leaves all clocks powered down.
 *
 *  Calls to si5351_set_freq() set one output clock only: it must be called once for each clock that will be used.
 *  Unused clocks will remain powered down. Setting the frequency of a clock also enables that clock's output.
 *
 *  The Si5351 integrated circuit places certain limitations on the ranges and combinations of frequencies that be
 *  assigned to each of the three clock outputs. It is the library user's responsibility to be sufficiently familiar
 *  with the Si5351 specification so as to avoid illegal settings.
 *
 ****************************************************************************************************************/

/***************************************************************************************************************
 * These definitions affect compiled code size as well as debugging and error checking functionality.
 *
 * Debug statements should be commented out in production code
 #define DEBUG_WITHOUT_I2C
 #define DEBUGGING_ONLY
 *
 * Enable the following definitions as needed, but check program memory usage.
 *
#define SUPPORT_FOUT_BELOW_1024KHZ
#define DO_BOUNDS_CHECKING
#define DIVIDE_XTAL_FREQ_IF_NEEDED
#define APPLY_XTAL_CALIBRATION_VALUE
#define SUPPORT_STATUS_READS
*/
#define PREVENT_UNACHIEVABLE_FREQUENCIES
/*
 * The following flag is used to disable GCC compiler optimizations in code regions where the optimizer has
 * been found to introduce run-time problems. Comment out the following #define if your compiler does not support
 * the syntax used in this library.
 */
#ifndef SELECTIVELY_DISABLE_OPTIMIZATION
	#define SELECTIVELY_DISABLE_OPTIMIZATION
#endif
/*
 ****************************************************************************************************************/

#define SI5351_XTAL_FREQ                                25000000UL
#define SI5351_PLL_FIXED                                900000000UL

#define SI5351_PLL_VCO_MIN                            600000000UL
//#define SI5351_PLL_VCO_MIN                              444500000UL
#define SI5351_PLL_VCO_MAX                              900000000UL /* This must be defined as an even number to support frequency-setting algorithm */
#define SI5351_MULTISYNTH_MIN_FREQ                      1000000UL
#define SI5351_MULTISYNTH_DIVBY4_FREQ                   150000000UL
#define SI5351_MULTISYNTH_MAX_FREQ                      160000000UL
#define SI5351_MULTISYNTH_SHARE_MAX                     112500000UL
#define SI5351_MULTISYNTH67_MAX_FREQ                    SI5351_MULTISYNTH_DIVBY4_FREQ
#define SI5351_CLKOUT_MIN_FREQ                          8000UL
#define SI5351_CLKOUT_MAX_FREQ                          SI5351_MULTISYNTH_MAX_FREQ
#define SI5351_CLKOUT67_MAX_FREQ                        SI5351_MULTISYNTH67_MAX_FREQ
#define SI5351_CLKIN_MAX_FREQ							10000000
#define SI5351_CLKIN_MIN_FREQ							40000000

#define SI5351_PLL_A_MIN                                15
#define SI5351_PLL_A_MAX                                90
#define SI5351_PLL_B_MAX                                (SI5351_PLL_C_MAX - 1)
#define SI5351_PLL_C_MAX                                1048575
#define SI5351_MULTISYNTH_A_MIN                         6
#define SI5351_MULTISYNTH_A_MAX                         1800
#define SI5351_MULTISYNTH67_A_MAX                       254
#define SI5351_MULTISYNTH_B_MAX                         (SI5351_MULTISYNTH_C_MAX - 1)
#define SI5351_MULTISYNTH_C_MAX                         1048575
#define SI5351_MULTISYNTH_P1_MAX                        ((1 << 18) - 1)
#define SI5351_MULTISYNTH_P2_MAX                        ((1 << 20) - 1)
#define SI5351_MULTISYNTH_P3_MAX                        ((1 << 20) - 1)

#define SI5351_DEVICE_STATUS                            0
#define SI5351_INTERRUPT_STATUS                         1
#define SI5351_INTERRUPT_MASK                           2
#define SI5351_STATUS_SYS_INIT                          (1 << 7)
#define SI5351_STATUS_LOL_B                             (1 << 6)
#define SI5351_STATUS_LOL_A                             (1 << 5)
#define SI5351_STATUS_LOS                               (1 << 4)
#define SI5351_OUTPUT_ENABLE_CTRL                       3
#define SI5351_OEB_PIN_ENABLE_CTRL                      9
#define SI5351_PLL_INPUT_SOURCE                         15
#define SI5351_CLKIN_DIV_MASK                           (3 << 6)
#define SI5351_CLKIN_DIV_1                              (0 << 6)
#define SI5351_CLKIN_DIV_2                              (1 << 6)
#define SI5351_CLKIN_DIV_4                              (2 << 6)
#define SI5351_CLKIN_DIV_8                              (3 << 6)
#define SI5351_PLLB_SOURCE                              (1 << 3)
#define SI5351_PLLA_SOURCE                              (1 << 2)

#define SI5351_CLK0_CTRL                                16
#define SI5351_CLK1_CTRL                                17
#define SI5351_CLK2_CTRL                                18
#define SI5351_CLK3_CTRL                                19
#define SI5351_CLK4_CTRL                                20
#define SI5351_CLK5_CTRL                                21
#define SI5351_CLK6_CTRL                                22
#define SI5351_CLK7_CTRL                                23
#define SI5351_CLK_POWERDOWN                            (1 << 7)
#define SI5351_CLK_INTEGER_MODE                         (1 << 6)
#define SI5351_CLK_PLL_SELECT                           (1 << 5)
#define SI5351_CLK_INVERT                               (1 << 4)
#define SI5351_CLK_INPUT_MASK                           (3 << 2)
#define SI5351_CLK_INPUT_XTAL                           (0 << 2)
#define SI5351_CLK_INPUT_CLKIN                          (1 << 2)
#define SI5351_CLK_INPUT_MULTISYNTH_0_4                 (2 << 2)
#define SI5351_CLK_INPUT_MULTISYNTH_N                   (3 << 2)
#define SI5351_CLK_DRIVE_STRENGTH_MASK                  (3 << 0)
#define SI5351_CLK_DRIVE_STRENGTH_2MA                   (0 << 0)
#define SI5351_CLK_DRIVE_STRENGTH_4MA                   (1 << 0)
#define SI5351_CLK_DRIVE_STRENGTH_6MA                   (2 << 0)
#define SI5351_CLK_DRIVE_STRENGTH_8MA                   (3 << 0)

#define SI5351_CLK3_0_DISABLE_STATE                     24
#define SI5351_CLK7_4_DISABLE_STATE                     25
#define SI5351_CLK_DISABLE_STATE_MASK                   3
#define SI5351_CLK_DISABLE_STATE_LOW                    0
#define SI5351_CLK_DISABLE_STATE_HIGH                   1
#define SI5351_CLK_DISABLE_STATE_FLOAT                  2
#define SI5351_CLK_DISABLE_STATE_NEVER                  3

#define SI5351_PARAMETERS_LENGTH                        8
#define SI5351_PLLA_MULTISYNTH_FEEDBACK_PARAMETERS      26
#define SI5351_PLLB_MULTISYNTH_FEEDBACK_PARAMETERS      34
#define SI5351_MS0_PARAMETERS                           42
#define SI5351_MS1_PARAMETERS                           50
#define SI5351_MS2_PARAMETERS                           58
#define SI5351_MS3_PARAMETERS                           66
#define SI5351_MS4_PARAMETERS                           74
#define SI5351_MS5_PARAMETERS                           82
#define SI5351_MS6_PARAMETERS                           90
#define SI5351_MS7_PARAMETERS                           91
#define SI5351_CLK6_7_OUTPUT_DIVIDER                    92
#define SI5351_OUTPUT_CLK_DIV_MASK                      (7 << 4)
#define SI5351_OUTPUT_CLK6_DIV_MASK                     (7 << 0)
#define SI5351_OUTPUT_CLK_DIV_SHIFT                     4
#define SI5351_OUTPUT_CLK_DIV6_SHIFT                    0
#define SI5351_OUTPUT_CLK_DIV_1                         0
#define SI5351_OUTPUT_CLK_DIV_2                         1
#define SI5351_OUTPUT_CLK_DIV_4                         2
#define SI5351_OUTPUT_CLK_DIV_8                         3
#define SI5351_OUTPUT_CLK_DIV_16                        4
#define SI5351_OUTPUT_CLK_DIV_32                        5
#define SI5351_OUTPUT_CLK_DIV_64                        6
#define SI5351_OUTPUT_CLK_DIV_128                       7
#define SI5351_OUTPUT_CLK_DIVBY4                        (3 << 2)

#define SI5351_SSC_PARAM0                               149
#define SI5351_SSC_PARAM1                               150
#define SI5351_SSC_PARAM2                               151
#define SI5351_SSC_PARAM3                               152
#define SI5351_SSC_PARAM4                               153
#define SI5351_SSC_PARAM5                               154
#define SI5351_SSC_PARAM6                               155
#define SI5351_SSC_PARAM7                               156
#define SI5351_SSC_PARAM8                               157
#define SI5351_SSC_PARAM9                               158
#define SI5351_SSC_PARAM10                              159
#define SI5351_SSC_PARAM11                              160
#define SI5351_SSC_PARAM12                              161

#define SI5351_VXCO_PARAMETERS_LOW                      162
#define SI5351_VXCO_PARAMETERS_MID                      163
#define SI5351_VXCO_PARAMETERS_HIGH                     164

#define SI5351_CLK0_PHASE_OFFSET                        165
#define SI5351_CLK1_PHASE_OFFSET                        166
#define SI5351_CLK2_PHASE_OFFSET                        167
#define SI5351_CLK3_PHASE_OFFSET                        168
#define SI5351_CLK4_PHASE_OFFSET                        169
#define SI5351_CLK5_PHASE_OFFSET                        170

#define SI5351_PLL_RESET                                177
#define SI5351_PLL_RESET_B                              (1 << 7)
#define SI5351_PLL_RESET_A                              (1 << 5)

#define SI5351_CRYSTAL_LOAD                             183
#define SI5351_CRYSTAL_LOAD_MASK                        (3 << 6)

#define SI5351_FANOUT_ENABLE                            187
#define SI5351_CLKIN_ENABLE                             (1 << 7)
#define SI5351_XTAL_ENABLE                              (1 << 6)
#define SI5351_MULTISYNTH_ENABLE                        (1 << 4)

/* Macro definitions */

#define RFRAC_DENOM                                     ((1L << 20) - 1)

#ifdef DEBUGGING_ONLY

#define NUM_REGS_MAX 100

	typedef struct Reg_Data
	{
		unsigned char Reg_Addr;
		unsigned char Reg_Val;
	} Reg_Data;

#endif  /* #ifdef DEBUGGING_ONLY */


/********************************************************************************************************************
 * Typedefs
 ******************************************************************************************************************** */


#ifndef Frequency_Hz
	typedef uint32_t Frequency_Hz;
#endif

#define FREQUENCY_NOT_SPECIFIED 0

	typedef enum si5351_xtal_load_pF
	{
		SI5351_CRYSTAL_LOAD_6PF = (uint8_t)(1 << 6),
		SI5351_CRYSTAL_LOAD_8PF = (uint8_t)(2 << 6),
		SI5351_CRYSTAL_LOAD_10PF = (uint8_t)(3 << 6)
	} Si5351_Xtal_load_pF;

	typedef enum si5351_clock
	{
		SI5351_CLK0 = 0,
		SI5351_CLK1 = 1,
		SI5351_CLK2 = 2,
		NUMBER_OF_SI5351_CLOCKS,
		SI5351_NO_CLOCK
	} Si5351_clock;

	typedef enum si5351_clk_enable
	{
		SI5351_CLK_DISABLED = 0,
		SI5351_CLK_ENABLED,
		SI5351_ENABLE_NOT_SPECIFIED
	} Si5351_clock_enable;

	typedef enum si5351_pll
	{
		SI5351_PLLA = 1,
		SI5351_PLLB = 2,
		SI5351_PLLA_B = 3
	} Si5351_pll;

	typedef enum si5351_drive
	{
		SI5351_DRIVE_2MA = 0,
		SI5351_DRIVE_4MA,
		SI5351_DRIVE_6MA,
		SI5351_DRIVE_8MA,
		SI5351_DRIVE_NOT_SPECIFIED
	} Si5351_drive;

	typedef struct Parameters32bit
	{
		uint32_t p1;
		uint32_t p2;
		uint32_t p3;
	} Parameters32bit;

	typedef struct Registers8bit
	{
		uint8_t p1_0;
		uint8_t p1_1;
		uint8_t p1_2;
		uint8_t p1_3;
		uint8_t p2_0;
		uint8_t p2_1;
		uint8_t p2_2;
		uint8_t p2_3;
		uint8_t p3_0;
		uint8_t p3_1;
		uint8_t p3_2;
		uint8_t p3_3;
	} Registers8bit;


	/* Create a union to facilitate storing 32-bit calculated parameters
	and reading them out as 8-bit register values. This approach reduces the
	amount of shifting and masking required to obtain the register values */
	typedef union u_si5351_regs
	{
		Registers8bit register8b;
		Parameters32bit parameter32b;
	} Union_si5351_regs;

/********************************************************************************************************************
 * Public Function Prototypes
 ******************************************************************************************************************** */
#ifdef INCLUDE_SI5351_SUPPORT

/**
 */
void si5351_shutdown_comms(void);

/**
 */
EC si5351_shutdown(void);


/**
 */
void si5351_start_comms(void);

/**
 */
bool si5351_init(Si5351_Xtal_load_pF, Frequency_Hz);
EC si5351_init_for_quad(Frequency_Hz freq_Fout);
EC si5351_set_quad_frequency(Frequency_Hz freq_Fout);
uint8_t si5351_get_status(void);

/**
 */
Frequency_Hz si5351_get_frequency(Si5351_clock clock);

/**
 */
EC si5351_clock_enable(Si5351_clock, bool);

/**
 */
EC si5351_drive_strength(Si5351_clock, Si5351_drive);

/**
 */
void si5351_set_correction(int32_t);

/**
 */
int32_t si5351_get_correction(void);

#ifdef SUPPORT_STATUS_READS
/**
 */
void si5351_read_status(void);
#endif  /* #ifdef SUPPORT_STATUS_READS */

#ifdef DEBUGGING_ONLY

/**
 */
bool compare_with_register_map(void);

/**
 */
void dump_registers(void);

#endif  /* #ifdef DEBUGGING_ONLY */

#endif  /* #ifdef INCLUDE_SI5351_SUPPORT */

#ifdef __cplusplus
}
#endif

#endif  /* SI5351_H_ */
