OpenARDF/SignalSnagger/Software/AVR128DA48/SignalSnagger/src/si5351.cpp

/*
 *  MIT License
 *
 *  Copyright (c) 2022 DigitalConfections
 *
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
 * si5353.c
 *
 */

#include "defs.h"

#ifdef INCLUDE_SI5351_SUPPORT

#include <stdio.h>
#include <stdint.h>
#include <stdlib.h>
#include <string.h>
#include <math.h>
#include <util/twi.h>

#include "include/i2c.h"
#include "include/si5351.h"

#define SI5351_EVEN_INTEGER_FEEDBACK					 126

/*******************************
 * Global Variables
 ********************************/
	static int32_t g_si5351_ref_correction = EEPROM_SI5351_CALIBRATION_DEFAULT;
	static Frequency_Hz freqVCOB = 0;

	static Frequency_Hz g_xtal_freq = SI5351_XTAL_FREQ;
	static uint8_t enabledClocksMask = 0x00;
	static Frequency_Hz clock_out[3] = { 0, 0, 0 };
		
#ifdef DEBUGGING_ONLY
/* Paste ClockBuilder-generated register values below. These will */
/* be compared with what this library generates. */
		Reg_Data const Reg_Store[NUM_REGS_MAX] = {
			{ 15,  0x00 },
			{ 16,  0x4C },
			{ 17,  0x2C },
			{ 18,  0x6C },
			{ 19,  0x80 },
			{ 20,  0x80 },
			{ 21,  0x80 },
			{ 22,  0x80 },
			{ 23,  0xC0 },
			{ 24,  0x00 },
			{ 25,  0x00 },
			{ 26,  0x00 },
			{ 27,  0x7D },
			{ 28,  0x00 },
			{ 29,  0x0D },
			{ 30,  0xFE },
			{ 31,  0x00 },
			{ 32,  0x00 },
			{ 33,  0x7A },
			{ 34,  0x00 },
			{ 35,  0x01 },
			{ 36,  0x00 },
			{ 37,  0x0C },
			{ 38,  0x00 },
			{ 39,  0x00 },
			{ 40,  0x00 },
			{ 41,  0x00 },
			{ 42,  0x00 },
			{ 43,  0x01 },
			{ 44,  0x00 },
			{ 45,  0x01 },
			{ 46,  0x00 },
			{ 47,  0x00 },
			{ 48,  0x00 },
			{ 49,  0x00 },
			{ 50,  0x00 },
			{ 51,  0x6B },
			{ 52,  0x00 },
			{ 53,  0x1E },
			{ 54,  0xB5 },
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
		};
#endif  /* #ifdef DEBUGGING_ONLY */

/*******************************
 * Private function prototypes
 ********************************/
			
	EC si5351_pll_reset(Si5351_pll pll);

#ifdef APPLY_XTAL_CALIBRATION_VALUE
	bool pll_output_ms_calc(Frequency_Hz, Frequency_Hz, Union_si5351_regs *, int32_t);
#else
	bool pll_output_ms_calc(Frequency_Hz, Frequency_Hz, Union_si5351_regs *);
#endif

#ifdef SUPPORT_FOUT_BELOW_1024KHZ
		uint8_t select_r_div(Frequency_Hz *);
#endif

	uint32_t multisynth_feedback_calc(Frequency_Hz, Si5351_pll, Union_si5351_regs *, bool *, bool *);

	bool set_pll(Frequency_Hz, Frequency_Hz, Si5351_pll);

	bool set_multisynth_registers_source(Si5351_clock, Si5351_pll);
	bool set_multisynth_registers(Si5351_clock clk, Union_si5351_regs ms_reg, bool int_mode, uint8_t r_div, bool div_by_4);
	uint32_t calc_gcd(uint32_t, uint32_t);
	void reduce_by_gcd(uint32_t *, uint32_t *);
	bool si5351_write_bulk(uint8_t, uint8_t *, uint8_t);
	bool si5351_read_bulk(uint8_t, uint8_t *, uint8_t);
	bool set_integer_mode(Si5351_clock, bool);
	bool ms_div(Si5351_clock, uint8_t, bool);
	EC si5351_set_phase90(Frequency_Hz fout, Frequency_Hz vco);
	EC si5351_get_phase(Si5351_clock clk, uint8_t* phase);
	EC si5351_set_CLK1_phase(uint8_t steps);
	

bool g_si5351_initialized = false;

EC si5351_shutdown(void)
{
	uint8_t data[2];

	/* Block 1: Disable Outputs */
	/* Set CLKx_DIS high; Reg. 3 = 0xFF */
	data[0] = 0xFF; // ~enabledClocksMask | 0xF9;
	si5351_write_bulk(SI5351_OUTPUT_ENABLE_CTRL, data, 1); /*  disable all clock outputs */

	/* Block 2: */
	/* Power down all output drivers */
	/* Reg. 16, 17, 18, 19, 20, 21, 22, 23 = 0x8C */
	data[0] = 0x8C;
	si5351_write_bulk(SI5351_CLK0_CTRL, data, 1); // power down all clocks */
	si5351_write_bulk(SI5351_CLK1_CTRL, data, 1);
	si5351_write_bulk(SI5351_CLK2_CTRL, data, 1);
	si5351_write_bulk(SI5351_CLK3_CTRL, data, 1);
	si5351_write_bulk(SI5351_CLK4_CTRL, data, 1);
	si5351_write_bulk(SI5351_CLK5_CTRL, data, 1);
	si5351_write_bulk(SI5351_CLK6_CTRL, data, 1);
	si5351_write_bulk(SI5351_CLK7_CTRL, data, 1);
	
	return(ERROR_CODE_NO_ERROR);
}

	
/*
 * bool si5351_init_for_quad(Frequency_Hz freq_Fout, Si5351_clock clk, bool clocksOff)
 *
 * Sets CLK0 and CLK1 operating in quadrature at the specified frequency
 *
 * freq - Output frequency in Hz
 *
 * Returns an error code
 *
 */
	EC si5351_init_for_quad(Frequency_Hz freq_Fout)
	{
		Union_si5351_regs ms_reg;
		uint8_t i;
		uint32_t a, b, c;
		uint32_t bx128;
		uint32_t bx128overc;

		uint8_t params[10];
		Frequency_Hz freq_VCO = 0;
		Si5351_pll target_pll = SI5351_PLLA;
		uint8_t data[2];

		if(!g_si5351_initialized) return(ERROR_CODE_NO_ERROR);
				
/******************************************************************************************/
		
		/* Block 1: Disable Outputs */
		/* Set CLKx_DIS high; Reg. 3 = 0xFF */
 		data[0] = 0xFF; // ~enabledClocksMask | 0xF9;
		si5351_write_bulk(SI5351_OUTPUT_ENABLE_CTRL, data, 1); /*  disable all clock outputs */

		clock_out[SI5351_CLK0] = freq_Fout; /* store the value for quick reference */
		clock_out[SI5351_CLK1] = freq_Fout;

		/* https://www.skyworksinc.com/-/media/Skyworks/SL/documents/public/application-notes/AN619.pdf */
		/* Page 19 */
		/* I2C Programming Procedure */
		/* */

		
/******************************************************************************************/
		
		/* Block 2: */
		/* Power down all output drivers */
		/* Reg. 16, 17, 18, 19, 20, 21, 22, 23 = 0x8C */
  		data[0] = 0x8C;
		si5351_write_bulk(SI5351_CLK0_CTRL, data, 1); // power down all clocks */
		si5351_write_bulk(SI5351_CLK1_CTRL, data, 1); 
		si5351_write_bulk(SI5351_CLK2_CTRL, data, 1); 
		si5351_write_bulk(SI5351_CLK3_CTRL, data, 1); 
		si5351_write_bulk(SI5351_CLK4_CTRL, data, 1); 
		si5351_write_bulk(SI5351_CLK5_CTRL, data, 1); 
		si5351_write_bulk(SI5351_CLK6_CTRL, data, 1); 
		si5351_write_bulk(SI5351_CLK7_CTRL, data, 1); 
		/*   o Drive strength = 2 mA */
		/*   o Input source = multisynth */
		/*   o Output clock not inverted */
		/*   o PLLA is multisynth source */
		/*   o Integer mode set */
		/*   o Clock powered down */
		/* If any of the above settings is incorrect, it needs to be set correctly in the code that follows. */

		
/******************************************************************************************/
/******************************************************************************************/
		
		/* Block 3: */
		/* Set interrupt masks */
		/* Ignore this for Si5153A */

		/* Block 4: */
		/* Write new configuration to device using */
		/* the contents of the register map */
		/* generated in software above. This */
		/* step also needs to power up the output drivers */
		/* (Registers 15-92 and 149-170 and 183) */

		freq_VCO = SI5351_EVEN_INTEGER_FEEDBACK*freq_Fout;
	
		/* Set multisynth registers (MS must be set before PLL) */
		if(set_multisynth_registers_source(SI5351_CLK0, target_pll))
		{
			return(ERROR_CODE_CLKGEN_NONRESPONSIVE);
		}
		
		if(set_multisynth_registers_source(SI5351_CLK1, target_pll))
		{
			return(ERROR_CODE_CLKGEN_NONRESPONSIVE);
		}
				
		/* Set PLL */

		/* Set integer part of feedback equation to an even integer between 4 and 126 */
		a = SI5351_EVEN_INTEGER_FEEDBACK;

		/* Find best approximation for b/c = fVCO mod fIN */
		b = 0;
		c = 0;

		bx128 = b << 7;
		bx128overc = 0; // bx128 / c;
		
		/* Write the 32-bit parameters into the union */
		ms_reg.parameter32b.p1 = (uint32_t)((a << 7) + bx128overc) - 512;   /* 128 * a + floor((128 * b) / c) - 512 */
		ms_reg.parameter32b.p2 = (uint32_t)bx128 - (c * bx128overc);        /* 128 * b - c * floor((128 * b) / c) */
		ms_reg.parameter32b.p3 = c;
		
		/* Read the 8-bit register values out of the union */
		/* Registers 42-43 for CLK0; 50-51 for CLK1 */
		i=0;
		params[i++] = ms_reg.register8b.p3_1; /* MS0_P3[15:8] MultiSynth0 Divider AN619 p.33 */
		params[i++] = ms_reg.register8b.p3_0; /* MS0_P3[7:0] MultiSynth0 Divider AN619 p.33 */

		/* Register 44 for CLK0; 52 for CLK1 */
		params[i++] = ms_reg.register8b.p1_2 & 0x03;

		/* Registers 45-46 for CLK0 */
		params[i++] = ms_reg.register8b.p1_1; /* MS0_P1[15:8] MultiSynth0 Parameter 1 AN619 p.34 */
		params[i++] = ms_reg.register8b.p1_0;

		/* Register 47 for CLK0 */
		params[i] = (ms_reg.register8b.p3_2 << 4);
		params[i++] += (ms_reg.register8b.p2_2 & 0x0F);

		/* Registers 48-49 for CLK0 */
		params[i++] = ms_reg.register8b.p2_1;
		params[i++] = ms_reg.register8b.p2_0;

		/* Write the parameters */
		if(si5351_write_bulk(SI5351_MS0_PARAMETERS, params, i))
		{
			return(ERROR_CODE_CLKGEN_NONRESPONSIVE);
		}

		if(si5351_write_bulk(SI5351_MS1_PARAMETERS, params, i))
		{
			return(ERROR_CODE_CLKGEN_NONRESPONSIVE);
		}
		
/******************************************************************************************/
/******************************************************************************************/
		
		a = freq_VCO / g_xtal_freq;
		b = freq_VCO % g_xtal_freq;
		c = g_xtal_freq;	
		
		reduce_by_gcd(&b, &c);

		bx128 = b << 7;
		bx128overc = bx128 / c;

		/* Write the 32-bit parameters into the union */
		ms_reg.parameter32b.p1 = (uint32_t)((a << 7) + bx128overc) - 512;   /* 128 * a + floor((128 * b) / c) - 512 */
		ms_reg.parameter32b.p2 = (uint32_t)bx128 - (c * bx128overc);        /* 128 * b - c * floor((128 * b) / c) */
		ms_reg.parameter32b.p3 = c;

		/* Read the 8-bit register values out of the union */
		/* Registers 26-27 */
		i=0;
		params[i++] = ms_reg.register8b.p3_1;			/* MSNA_P3[15:8] */
		params[i++] = ms_reg.register8b.p3_0;			/* MSNA_P3[7:0]  */

		/* Register 28 */
		params[i++] = ms_reg.register8b.p1_2 & 0x03;	/* [XXXXNN] : MSNA_P1[17:16]  */

		/* Registers 29-30 */
		params[i++] = ms_reg.register8b.p1_1;			/* MSNA_P1[15:8] */
		params[i++] = ms_reg.register8b.p1_0;			/* MSNA_P1[7:0] */

		/* Register 31 */
		params[i] = ms_reg.register8b.p3_2 << 4;		/* MSNA_P3[19:16] : MSNA_P2[19:16] */
		params[i++] += ms_reg.register8b.p2_2 & 0x0F;

		/* Registers 32-33 */
		params[i++] = ms_reg.register8b.p2_1;			/* MSNA_P2[15:8] */
		params[i++] = ms_reg.register8b.p2_0;			/* MSNA_P2[7:0] */

		/* Write the parameters */
		if(si5351_write_bulk(SI5351_PLLA_MULTISYNTH_FEEDBACK_PARAMETERS, params, i))
		{
			return(ERROR_CODE_CLKGEN_NONRESPONSIVE);
		}
		
/******************************************************************************************/	
		
		set_integer_mode(SI5351_CLK0, false);
		set_integer_mode(SI5351_CLK1, false);

/******************************************************************************************/
				
		si5351_set_CLK1_phase(SI5351_EVEN_INTEGER_FEEDBACK); /* affects only SI5351_CLK1 */
	
/******************************************************************************************/
		
		/* Block 6: */
		/* Enable desired outputs */
		/* (see Register 3) */
		uint8_t enabledClocksMask = 0x03;
 		data[0] = ~enabledClocksMask;
 		if(si5351_write_bulk(SI5351_OUTPUT_ENABLE_CTRL, data, 1))  /* enable clock(s) in use */
		{
			return(ERROR_CODE_CLKGEN_NONRESPONSIVE);
		} 
		
		/* power up the clocks */
		data[0] = 0x0C;
 		if(si5351_write_bulk(SI5351_CLK0_CTRL, data, 1))  /* power up only clock being set, leaving that clock configured as follows: */
		{
			return(ERROR_CODE_CLKGEN_NONRESPONSIVE);
		} 
			
 		data[0] = 0x0C;
 		if(si5351_write_bulk(SI5351_CLK1_CTRL, data, 1))  /* power up only clock being set, leaving that clock configured as follows: */
		{
			return(ERROR_CODE_CLKGEN_NONRESPONSIVE);
		} 
		/*   o Drive strength = 2 mA */
		/*   o Input source = multisynth */
		/*   o Output clock not inverted */
		/*   o PLLA is multisynth source */
		/*   o Integer mode off */
		/*   o Clock powered up */

		si5351_pll_reset(SI5351_PLLA);
		return(ERROR_CODE_NO_ERROR);
	}


	EC si5351_set_quad_frequency(Frequency_Hz freq_Fout)
	{
		uint8_t i = 0;
		uint32_t a, b, c;
		uint8_t params[10];
		Union_si5351_regs ms_reg;
		Frequency_Hz freq_VCO = 0;

		if(!g_si5351_initialized) return(ERROR_CODE_NO_ERROR);
		
		Frequency_Hz freq = freq_Fout;

		clock_out[SI5351_CLK0] = freq_Fout; /* store the value for quick reference */
		clock_out[SI5351_CLK1] = freq_Fout;

		/* https://www.skyworksinc.com/-/media/Skyworks/SL/documents/public/application-notes/AN619.pdf */

		freq_VCO = SI5351_EVEN_INTEGER_FEEDBACK*freq;
		
		a = freq_VCO / g_xtal_freq;
		b = freq_VCO % g_xtal_freq;
		c = g_xtal_freq;	
		
		reduce_by_gcd(&b, &c);

		uint32_t bx128 = b << 7;
		uint32_t bx128overc = bx128 / c;

		/* Write the 32-bit parameters into the union */
		ms_reg.parameter32b.p1 = (uint32_t)((a << 7) + bx128overc) - 512;   /* 128 * a + floor((128 * b) / c) - 512 */
		ms_reg.parameter32b.p2 = (uint32_t)bx128 - (c * bx128overc);        /* 128 * b - c * floor((128 * b) / c) */
		ms_reg.parameter32b.p3 = c;
		
#ifdef DO_BOUNDS_CHECKING
		if(a < SI5351_PLL_A_MIN)
		{
			return(true);
		}
		
		if(a > SI5351_PLL_A_MAX)
		{
			return(true);
		}
#endif

		/* Read the 8-bit register values out of the union */
		/* Registers 26-27 */
		params[i++] = ms_reg.register8b.p3_1;
		params[i++] = ms_reg.register8b.p3_0;

		/* Register 28 */
		params[i++] = ms_reg.register8b.p1_2 & 0x03;

		/* Registers 29-30 */
		params[i++] = ms_reg.register8b.p1_1;
		params[i++] = ms_reg.register8b.p1_0;

		/* Register 31 */
		params[i] = ms_reg.register8b.p3_2 << 4;
		params[i++] += ms_reg.register8b.p2_2 & 0x0F;

		/* Registers 32-33 */
		params[i++] = ms_reg.register8b.p2_1;
		params[i++] = ms_reg.register8b.p2_0;

		/* Write the parameters */
			
		if(si5351_write_bulk(SI5351_PLLA_MULTISYNTH_FEEDBACK_PARAMETERS, params, i))
		{
			return(ERROR_CODE_CLKGEN_NONRESPONSIVE);
		}

		return(ERROR_CODE_NO_ERROR);
	}

/*///////////////////////////////////////////////////////////////////////////////////////////////////////////////////// */
/* Public functions */
/*///////////////////////////////////////////////////////////////////////////////////////////////////////////////////// */

	void si5351_shutdown_comms(void)
	{
		I2C_0_Shutdown();
	}

	void si5351_start_comms(void)
	{
		I2C_0_Init();
	}

/*
 * init(Si5351_Xtal_load_pF xtal_load_c, Frequency_Hz ref_osc_freq)
 *
 * Setup communications to the Si5351 and set the crystal
 * load capacitance.
 *
 * xtal_load_c - Crystal load capacitance.
 * ref_osc_freq - Crystal/reference oscillator frequency (Hz).
 *
 */
	bool si5351_init(Si5351_Xtal_load_pF xtal_load_c, Frequency_Hz ref_osc_freq)
	{
		static bool err = false;
		uint8_t data[2];
		
#ifndef DEBUG_WITHOUT_I2C
			/* Start I2C comms */
			I2C_0_Init();
#endif

#ifdef DEBUGGING_ONLY
			uint8_t result_val = 0x00;
			bool result = false;
#endif
		uint8_t reg_val;

		freqVCOB = 0;
		g_xtal_freq = SI5351_XTAL_FREQ;
		enabledClocksMask = 0x00;

		/* Disable Outputs */
		/* Set CLKx_DIS high; Reg. 3 = 0xFF */
		data[0] = 0xFF;
		err = si5351_write_bulk(0x03, data, 1);
		
		if(err) return err;
		/* Power down clocks */
		data[0] = 0xCC;
		err |= si5351_write_bulk(0x10, data, 1);
		err |= si5351_write_bulk(0x11, data, 1);
		err |= si5351_write_bulk(0x12, data, 1);

		/* Set crystal load capacitance */
		reg_val = 0x12; /* 0b010010 reserved value bits */
		reg_val |= xtal_load_c;

		data[0] = reg_val;
		err |= si5351_write_bulk(SI5351_CRYSTAL_LOAD, data, 1);

		if(!ref_osc_freq)
		{
			ref_osc_freq = SI5351_XTAL_FREQ;
		}

		/* Change the ref osc freq if different from default */
		if(ref_osc_freq != g_xtal_freq)
		{
			if(si5351_read_bulk(SI5351_PLL_INPUT_SOURCE, data, 1))
			{
				return true;
			}
			
			reg_val = data[0];

			/* Clear the bits first */
			reg_val &= ~(SI5351_CLKIN_DIV_MASK);

			g_xtal_freq = ref_osc_freq;
			reg_val |= SI5351_CLKIN_DIV_1;

#ifdef DIVIDE_XTAL_FREQ_IF_NEEDED
				/* Divide down if greater than 30 MHz */

				if(ref_osc_freq > 30000000UL && ref_osc_freq <= 60000000UL)
				{
					g_xtal_freq /= 2;
					reg_val |= SI5351_CLKIN_DIV_2;
				}
				else if(ref_osc_freq > 60000000UL && ref_osc_freq <= 100000000UL)
				{
					g_xtal_freq /= 4;
					reg_val |= SI5351_CLKIN_DIV_4;
				}

#endif  /* #ifndef DIVIDE_XTAL_FREQ_IF_NEEDED */

			data[0] = reg_val;
			err |= si5351_write_bulk(SI5351_PLL_INPUT_SOURCE, data, 1);
		}
		
		g_si5351_initialized = !err;

		return err;
	}
	

/*
 * Frequency_Hz si5351_get_freq(Si5351_clock output)
 *
 * Returns the clock frequency setting of the specified CLK output
 *
 * output - Clock output (use the si5351_clock enum)
 *
 * Returns true on failure
 *
 */
	Frequency_Hz si5351_get_frequency(Si5351_clock clock)
	{
		return(clock_out[clock]);
	}
	
/*
 * si5351 multisynth reset
 *
 */
EC si5351_pll_reset(Si5351_pll pll)
{
	uint8_t reg_val;
	uint8_t data[2];
		
	if(si5351_read_bulk(SI5351_PLL_RESET, data, 1)) 
	{
		return ERROR_CODE_RTC_NONRESPONSIVE;
	}
		
	reg_val = data[0];
	
	if(pll & SI5351_PLLA)
	{
		reg_val |= (SI5351_PLL_RESET_A);
	}
	
	if(pll & SI5351_PLLB)
	{
		reg_val |= (SI5351_PLL_RESET_B);
	}

	data[0] = reg_val;
	if(si5351_write_bulk(SI5351_PLL_RESET, data, 1)) return ERROR_CODE_RTC_NONRESPONSIVE;

	return ERROR_CODE_NO_ERROR;
}


/*
 * si5351_clock_enable(Si5351_clock clk, bool enable)
 *
 * Enable or disable a chosen clock
 * clk - Clock output
 * enable - 1 to enable, 0 to disable
 *
 */
	EC si5351_clock_enable(Si5351_clock clk, bool enable)
	{
		uint8_t reg_val;
		uint8_t data[2];
		
		if(si5351_read_bulk(SI5351_OUTPUT_ENABLE_CTRL, data, 1)) 
		{
			return ERROR_CODE_RTC_NONRESPONSIVE;
		}
		
		reg_val = data[0];

		if(enable)
		{
			reg_val &= ~(1 << (uint8_t)clk);
		}
		else
		{
			reg_val |= (1 << (uint8_t)clk);
		}

		data[0] = reg_val;
		if(si5351_write_bulk(SI5351_OUTPUT_ENABLE_CTRL, data, 1)) return ERROR_CODE_RTC_NONRESPONSIVE;

		return ERROR_CODE_NO_ERROR;
	}
	
	
	
/*
 * si5351_drive_strength(Si5351_clock clk, Si5351_drive drive)
 *
 * Sets the drive strength of the specified clock output
 *
 * clk - Clock output
 * drive - Desired drive level
 *
 */
	EC si5351_drive_strength(Si5351_clock clk, Si5351_drive drive)
	{
		uint8_t reg_val;
		uint8_t data[2];
		const uint8_t mask = 0x03;

		if(si5351_read_bulk(SI5351_CLK0_CTRL + (uint8_t)clk, data, 1))
		{
			return ERROR_CODE_CLKGEN_NONRESPONSIVE;
		}
		
		reg_val = data[0];

		switch(drive)
		{
			case SI5351_DRIVE_2MA:
			{
				reg_val &= ~(mask);
				reg_val |= 0x00;
			}
			break;

			case SI5351_DRIVE_4MA:
			{
				reg_val &= ~(mask);
				reg_val |= 0x01;
			}
			break;

			case SI5351_DRIVE_6MA:
			{
				reg_val &= ~(mask);
				reg_val |= 0x02;
			}
			break;

			case SI5351_DRIVE_8MA:
			{
				reg_val &= ~(mask);
				reg_val |= 0x03;
			}
			break;

			default:
			{
			}
			break;
		}

		data[0] = reg_val;
		if(si5351_write_bulk(SI5351_CLK0_CTRL + (uint8_t)clk, data, 1)) return ERROR_CODE_CLKGEN_NONRESPONSIVE;

		return ERROR_CODE_NO_ERROR;
	}
	
	
/*
 * si5351_set_phase(void)
 *
 * Sets the clock phase.
 *  https://www.skyworksinc.com/-/media/Skyworks/SL/documents/public/application-notes/AN619.pdf
 * CLKx_PHOFF[4:0] = Round( DesiredOffset(sec) x 4 x Fvco)
 */
	EC si5351_set_phase90(Frequency_Hz fout, Frequency_Hz vco)
	{
		EC err = ERROR_CODE_NO_ERROR;
		uint8_t reg_val;
		uint8_t data[2];
		const uint8_t mask = 0x7F;
		
		uint32_t offset = vco/fout;
		if(offset > mask)
		{
			err = ERROR_CODE_SW_LOGIC_ERROR;
			offset = mask;
		}
		
		reg_val = (uint8_t)offset & mask;
		data[0] = reg_val;
		if(si5351_write_bulk(SI5351_CLK0_CTRL + (uint8_t)SI5351_CLK1, data, 1)) return ERROR_CODE_CLKGEN_NONRESPONSIVE;

		return err;
	}
	
/*
 * si5351_get_phase(void)
 *
 * Returns the clock phase.
 *  https://www.skyworksinc.com/-/media/Skyworks/SL/documents/public/application-notes/AN619.pdf 
 * CLKx_PHOFF[4:0] = Round( DesiredOffset(sec) x 4 x Fvco)
 */
	EC si5351_get_phase(Si5351_clock clk, uint8_t* phase)
	{
		uint8_t data[2];

		if(si5351_read_bulk(SI5351_CLK0_CTRL + (uint8_t)clk, data, 1))
		{
			return ERROR_CODE_CLKGEN_NONRESPONSIVE;
		}
		
		if(phase) *phase = data[0];
		
		return ERROR_CODE_NO_ERROR;
	}

/*///////////////////////////////////////////////////////////////////////////////////////////////////////////////////// */
/* Private functions */
/*///////////////////////////////////////////////////////////////////////////////////////////////////////////////////// */

/*
 * uint8_t select_r_div(Frequency_Hz *freq)
 *
 * The R dividers can be used to generate frequencies below about 500 kHz. Each individual output R divider can be
 * set to 1, 2, 4, 8,....128 by writing the proper setting for Rx_DIV. Set this parameter to generate frequencies down to
 * 8kHz.
 */
#ifdef SUPPORT_FOUT_BELOW_1024KHZ
		uint8_t select_r_div(Frequency_Hz *freq)
		{
			uint8_t r_div = SI5351_OUTPUT_CLK_DIV_1;

			Frequency_Hz max_freq = SI5351_CLKOUT_MIN_FREQ * 128;

			if(*freq < max_freq)
			{
				/* Choose the correct R divider for output frequencies between 8 kHz and 1.024 MHz */
				if((*freq >= SI5351_CLKOUT_MIN_FREQ) && (*freq < SI5351_CLKOUT_MIN_FREQ * 2))
				{
					r_div = SI5351_OUTPUT_CLK_DIV_128;
					*freq *= 128UL;
				}
				else if((*freq >= SI5351_CLKOUT_MIN_FREQ * 2) && (*freq < SI5351_CLKOUT_MIN_FREQ * 4))
				{
					r_div = SI5351_OUTPUT_CLK_DIV_64;
					*freq *= 64UL;
				}
				else if((*freq >= SI5351_CLKOUT_MIN_FREQ * 4) && (*freq < SI5351_CLKOUT_MIN_FREQ * 8))
				{
					r_div = SI5351_OUTPUT_CLK_DIV_32;
					*freq *= 32UL;
				}
				else if((*freq >= SI5351_CLKOUT_MIN_FREQ * 8) && (*freq < SI5351_CLKOUT_MIN_FREQ * 16))
				{
					r_div = SI5351_OUTPUT_CLK_DIV_16;
					*freq *= 16UL;
				}
				else if((*freq >= SI5351_CLKOUT_MIN_FREQ * 16) && (*freq < SI5351_CLKOUT_MIN_FREQ * 32))
				{
					r_div = SI5351_OUTPUT_CLK_DIV_8;
					*freq *= 8UL;
				}
				else if((*freq >= SI5351_CLKOUT_MIN_FREQ * 32) && (*freq < SI5351_CLKOUT_MIN_FREQ * 64))
				{
					r_div = SI5351_OUTPUT_CLK_DIV_4;
					*freq *= 4UL;
				}
				else if((*freq >= SI5351_CLKOUT_MIN_FREQ * 64) && (*freq < SI5351_CLKOUT_MIN_FREQ * 128))
				{
					r_div = SI5351_OUTPUT_CLK_DIV_2;
					*freq *= 2UL;
				}
			}

			return(r_div);
		}
#endif  /*#ifdef SUPPORT_FOUT_BELOW_1024KHZ */


/*
 * set_pll(Frequency_Hz freq_OUT, Frequency_Hz freq_VCO, Si5351_pll target_pll)
 *
 * Set the specified PLL to a specific oscillation frequency
 *
 * freq_VCO - Desired PLL frequency
 * target_pll - Which PLL to set (use the si5351_pll enum)
 *
 */
	bool set_pll(Frequency_Hz freq_OUT, Frequency_Hz freq_VCO, Si5351_pll target_pll)
	{
		Union_si5351_regs pll_reg;
		uint8_t params[10];

		/* Output Multisynth Settings (Synthesis Stage 2) */
	#ifdef APPLY_XTAL_CALIBRATION_VALUE
		if(pll_output_ms_calc(freq_OUT, freq_VCO, &pll_reg, g_si5351_ref_correction))
		{
			return(true);
		}
	#else
		if(pll_output_ms_calc(freq_OUT, freq_VCO, &pll_reg))
		{
			return(true);
		}
	#endif

		/* Prepare an array for parameters to be written to */
		uint8_t i = 0;

		/* Registers 26-27 */
		params[i++] = pll_reg.register8b.p3_1;
		params[i++] = pll_reg.register8b.p3_0;

		/* Register 28 */
		params[i++] = pll_reg.register8b.p1_2 & 0x03;

		/* Registers 29-30 */
		params[i++] = pll_reg.register8b.p1_1;
		params[i++] = pll_reg.register8b.p1_0;

		/* Register 31 */
		params[i] = pll_reg.register8b.p3_2 << 4;
		params[i++] += pll_reg.register8b.p2_2 & 0x0F;

		/* Registers 32-33 */
		params[i++] = pll_reg.register8b.p2_1;
		params[i++] = pll_reg.register8b.p2_0;

		/* Write the parameters */
		if(target_pll == SI5351_PLLA)
		{
			if(si5351_write_bulk(SI5351_PLLA_MULTISYNTH_FEEDBACK_PARAMETERS, params, i))
			{
				return(true);
			}
		}
		else    /* if(target_pll == SI5351_PLLB) */
		{
			if(si5351_write_bulk(SI5351_PLLB_MULTISYNTH_FEEDBACK_PARAMETERS, params, i))
			{
				return(true);
			}
		}

		return(false);
	}


/*
 * si5351_set_correction(int32_t corr)
 *
 * Use this to set the oscillator correction factor. Caller
 * is responsible for storing an EEPROM value for this
 * if it is to be saved to non-volatile memory.
 *
 * This value is a signed 32-bit integer of the
 * parts-per-10 million value that the actual oscillation
 * frequency deviates from the specified frequency.
 *
 * Any desired test frequency within the normal range of the
 * Si5351 should be set, then the actual output frequency
 * should be measured as accurately as possible. The
 * difference between the measured and specified frequencies
 * should be calculated in Hertz, then multiplied by 10 in
 * order to get the parts-per-10 million value.
 *
 * Since the Si5351 itself has an intrinsic 0 PPM error, this
 * correction factor is good across the entire tuning range of
 * the Si5351. Once this calibration is done accurately, it
 * should not have to be done again for the same Si5351 and
 * crystal. The library will read the correction factor from
 * EEPROM during initialization for use by the tuning
 * algorithms.
 */
	void si5351_set_correction(int32_t corr)
	{
		g_si5351_ref_correction = corr;
	}


/*
 * si5351_get_correction(void)
 *
 * Returns the oscillator correction factor.
 */
	int32_t si5351_get_correction(void)
	{
		return(g_si5351_ref_correction);
	}

/*
 * bool pll_output_ms_calc(Frequency_Hz freq_OUT, Frequency_Hz vco_freq, Union_si5351_regs *reg)
 *
 * Returns true on failure
 *
 */
#ifdef APPLY_XTAL_CALIBRATION_VALUE
	bool pll_output_ms_calc(Frequency_Hz freq_OUT, Frequency_Hz vco_freq, Union_si5351_regs *reg, int32_t correction)
#else
	bool pll_output_ms_calc(Frequency_Hz freq_OUT, Frequency_Hz vco_freq, Union_si5351_regs *reg)
#endif
	{
		uint32_t a, b, c;
		
#ifdef APPLY_XTAL_CALIBRATION_VALUE
		Frequency_Hz ref_freq = g_xtal_freq;
		/* Factor calibration value into nominal crystal frequency */
		/* Measured in parts-per-billion */
		if(correction)
		{
			ref_freq += (int32_t)((((((int64_t)correction) << 31) / 1000000000LL) * ref_freq) >> 31);
		}
#endif

#ifdef DO_BOUNDS_CHECKING
		if(vco_freq < SI5351_PLL_VCO_MIN)
		{
			return(true);
		}
		if(vco_freq > SI5351_PLL_VCO_MAX)
		{
			return(true);
		}
#endif

		/* Determine integer part of feedback equation */
		a = vco_freq / freq_OUT;

		/* Find best approximation for b/c = fVCO mod fIN */
		b = vco_freq % freq_OUT;
		c = freq_OUT;

		reduce_by_gcd(&b, &c);

		uint32_t bx128 = b << 7;
		uint32_t bx128overc = bx128 / c;
		reg->parameter32b.p1 = (uint32_t)((a << 7) + bx128overc) - 512;   /* 128 * a + floor((128 * b) / c) - 512 */
		reg->parameter32b.p2 = (uint32_t)bx128 - (c * bx128overc);        /* 128 * b - c * floor((128 * b) / c) */
		reg->parameter32b.p3 = c;

		return(false);
	}

/*
 * uint32_t calc_gcd(uint32_t m, uint32_t n)
 *
 * Simple implementation of Euclid's Algorithm for calculating GCD of two uint32's
 *
 */
	void reduce_by_gcd(uint32_t *m, uint32_t *n)
	{
		uint32_t r;
		uint32_t b = *m;
		uint32_t c = *n;

		if(!b || !c)
		{
			return;
		}

		for(r = b % c; r; b = c, c = r, r = b % c)
		{
			;
		}

		if(c > 1)
		{
			*m /= c;
			*n /= c;
		}

		return;
	}
	
	
/*
 * Frequency_Hz multisynth_feedback_calc(Frequency_Hz, Si5351_pll, Union_si5351_regs *, bool *, bool *)
 *
 * Valid Multisynth divider ratios are 4, 6, 8, and any fractional value between 8 + 1/1,048,575 and 900 + 0/1.
 * This means that if any output is greater than 112.5 MHz (900 MHz/8), then this output frequency sets one
 * of the VCO frequencies.
 *
 * Notes: This implementation only supports even integer divider ratios 4 <= div <= 900.
 *        This implementation always sets *int_mode to false
 *
 * Returns zero on failure. Returns with int_mode and divBy4 set appropriately.
 *
 */
	Frequency_Hz multisynth_feedback_calc(Frequency_Hz osc_freq, Si5351_pll target_pll, Union_si5351_regs *ms_reg, bool *int_mode, bool *divBy4)
	{
		uint32_t a = 0;
		Frequency_Hz freq_VCO = 0;

		*int_mode = false;   /* must be false to support setting the phase */

#ifdef DO_BOUNDS_CHECKING
		/* All frequencies above 150 MHz must use divide by 4 */
		if((osc_freq > SI5351_CLKIN_MAX_FREQ) || (osc_freq < SI5351_CLKIN_MIN_FREQ))
		{
			/*No support provided for input clock frequencies outside this range */
			return(0);
		}
		else
#endif  /* DO_BOUNDS_CHECKING */
		{
			a = SI5351_PLL_VCO_MIN / osc_freq;
			a = a >> 1;
			a = a << 1; /* ensure a is even */
			uint32_t temp;
			uint8_t done = false;
			uint8_t success = false;
			
			/* Find the lowest valid VCO frequency that is an even integer multiple of the oscillator frequency */
			while(!done)
			{
				temp = a * osc_freq;
				
				if((temp >= SI5351_PLL_VCO_MIN) && (temp <= SI5351_PLL_VCO_MAX))
				{
					success = true;
					done = true;
				}
				else
				{
					if(temp >= SI5351_PLL_VCO_MAX)
					{
						done = true;
					}
					else
					{
						a += 2;
					}
				}
			}

			if(success)
			{
				freq_VCO = a * osc_freq;
			}
		}
		
#ifdef DO_BOUNDS_CHECKING
		if(a < SI5351_PLL_A_MIN)
		{
			return(true);
		}
			
		if(a > SI5351_PLL_A_MAX)
		{
			return(true);
		}
#endif


		*divBy4 = (a == 4);
		ms_reg->parameter32b.p1 = (uint32_t)(a << 7) - 512;  /* 128 * a + floor((128 * b) / c) - 512 */
		ms_reg->parameter32b.p2 = 0;                         /* 128 * b - c * floor((128 * b) / c) */
		ms_reg->parameter32b.p3 = 1;
		
// 		Union_si5351_regs pll_reg;
 		uint8_t params[10];

		/* Prepare an array for parameters to be written to */
		uint8_t i = 0;

		/* Registers 26-27 */
		params[i++] = ms_reg->register8b.p3_1;
		params[i++] = ms_reg->register8b.p3_0;

		/* Register 28 */
		params[i++] = ms_reg->register8b.p1_2 & 0x03;

		/* Registers 29-30 */
		params[i++] = ms_reg->register8b.p1_1;
		params[i++] = ms_reg->register8b.p1_0;

		/* Register 31 */
		params[i] = ms_reg->register8b.p3_2 << 4;
		params[i++] += ms_reg->register8b.p2_2 & 0x0F;

		/* Registers 32-33 */
		params[i++] = ms_reg->register8b.p2_1;
		params[i++] = ms_reg->register8b.p2_0;

		/* Write the parameters */
		if(target_pll == SI5351_PLLA)
		{
			if(si5351_write_bulk(SI5351_PLLA_MULTISYNTH_FEEDBACK_PARAMETERS, params, i))
			{
				return(true);
			}
		}
		else    /* if(target_pll == SI5351_PLLB) */
		{
			if(si5351_write_bulk(SI5351_PLLB_MULTISYNTH_FEEDBACK_PARAMETERS, params, i))
			{
				return(true);
			}
		}

		return(freq_VCO);
	}


	bool si5351_write_bulk(uint8_t regAddr, uint8_t *data, uint8_t bytes)
	{
		uint8_t tries = 5;
		bool fail;
		while(tries-- && (fail = I2C_0_SendData(SI5351_I2C_SLAVE_ADDR, regAddr, data, bytes) != bytes));
		return(fail);
	}

	bool si5351_read_bulk(uint8_t regAddr, uint8_t *data, uint8_t bytes)
	{
		uint8_t tries = 5;
		bool fail;
		while(tries-- && (fail = I2C_0_GetData(SI5351_I2C_SLAVE_ADDR, regAddr, data, bytes) != bytes));
		return(fail);
	}


/*
 * set_multisynth_registers_source(Si5351_clock clk, Si5351_pll pll)
 *
 * clk - Clock output (use the si5351_clock enum)
 * pll - Which PLL to use as the source (use the si5351_pll enum)
 *
 * Set the desired PLL source for a multisynth.
 *
 */
	bool set_multisynth_registers_source(Si5351_clock clk, Si5351_pll pll)
	{
		uint8_t reg_val;
		uint8_t data[2];
		
		if(si5351_read_bulk(SI5351_CLK0_CTRL + (uint8_t)clk, data, 1))
		{
			return(true);
		}
		
		reg_val = data[0];

		if(pll == SI5351_PLLA)
		{
			reg_val &= ~(SI5351_CLK_PLL_SELECT);
		}
		else if(pll == SI5351_PLLB)
		{
			reg_val |= SI5351_CLK_PLL_SELECT;
		}

		data[0] = reg_val;
		if(si5351_write_bulk(SI5351_CLK0_CTRL + (uint8_t)clk, data, 1))
		{
			return(true);
		}
		
		return(false);
	}


/*
 * set_multisynth_registers(Si5351_clock clk, Union_si5351_regs ms_reg, bool int_mode, uint8_t r_div, bool div_by_4)
 *
 * Set the specified multisynth parameters.
 *
 * clk - Clock output (use the si5351_clock enum)
 * int_mode - 1 to enable, 0 to disable
 * r_div - Desired r_div ratio
 * div_by_4 - 1 Divide By 4 mode: 0 to disable
 *
 */
	bool set_multisynth_registers(Si5351_clock clk, Union_si5351_regs ms_reg, bool int_mode, uint8_t r_div, bool div_by_4)
	{
		uint8_t params[11];
		uint8_t i = 0;
		uint8_t reg_val;
		uint8_t data[2];

		/* Registers 42-43 for CLK0; 50-51 for CLK1 */
		params[i++] = ms_reg.register8b.p3_1; /* MS0_P3[15:8] MultiSynth0 Divider AN619 p.33 */
		params[i++] = ms_reg.register8b.p3_0; /* MS0_P3[7:0] MultiSynth0 Divider AN619 p.33 */

		/* Register 44 for CLK0; 52 for CLK1 */
		if(si5351_read_bulk((SI5351_MS0_PARAMETERS + 2) + (clk * 8), data, 1))
		{
			return(true);
		}
		
		reg_val = data[0];

		reg_val &= 0xFC;    /*~(0x03); */
		params[i++] = reg_val | (ms_reg.register8b.p1_2 & 0x03);

		/* Registers 45-46 for CLK0 */
		params[i++] = ms_reg.register8b.p1_1; /* MS0_P1[15:8] MultiSynth0 Parameter 1 AN619 p.34 */
		params[i++] = ms_reg.register8b.p1_0;

		/* Register 47 for CLK0 */
		params[i] = (ms_reg.register8b.p3_2 << 4);
		params[i++] += (ms_reg.register8b.p2_2 & 0x0F);

		/* Registers 48-49 for CLK0 */
		params[i++] = ms_reg.register8b.p2_1;
		params[i++] = ms_reg.register8b.p2_0;

		/* Write the parameters */
		switch(clk)
		{
			case SI5351_CLK0:
			{
				if(si5351_write_bulk(SI5351_MS0_PARAMETERS, params, i))
				{
					return(true);
				}
			}
			break;

			case SI5351_CLK1:
			{
				if(si5351_write_bulk(SI5351_MS1_PARAMETERS, params, i))
				{
					return(true);
				}
			}
			break;

			case SI5351_CLK2:
			{
				if(si5351_write_bulk(SI5351_MS2_PARAMETERS, params, i))
				{
					return(true);
				}
			}
			break;

			default:
			{
			}
			break;
		}

		if(set_integer_mode(clk, int_mode))
		{
			return(true);
		}
		
		if(ms_div(clk, r_div, div_by_4))
		{
			return(true);
		}
		
		return(false);
	}


/*
 * set_integer_mode(Si5351_clock clk, bool int_mode)
 *
 * clk - Clock output (use the si5351_clock enum)
 * enable - 1 to enable, 0 to disable
 *
 * Set the indicated multisynth into integer mode.
 */
	bool set_integer_mode(Si5351_clock clk, bool enable)
	{
		uint8_t reg_val;
		uint8_t data[2];

		if(si5351_read_bulk(SI5351_CLK0_CTRL + (uint8_t)clk, data, 1))
		{
			return(true);
		}
		
		reg_val = data[0];

		if(enable)
		{
			reg_val |= (SI5351_CLK_INTEGER_MODE);
		}
		else
		{
			reg_val &= ~(SI5351_CLK_INTEGER_MODE);
		}

		data[0] = reg_val;
		return(si5351_write_bulk(SI5351_CLK0_CTRL + (uint8_t)clk, data, 1));
	}


	bool ms_div(Si5351_clock clk, uint8_t r_div, bool div_by_4)
	{
		uint8_t reg_val, reg_addr;
		uint8_t data[2];

		switch(clk)
		{
			case SI5351_CLK0:
			{
				reg_addr = SI5351_MS0_PARAMETERS + 2;
			}
			break;

			case SI5351_CLK1:
			{
				reg_addr = SI5351_MS1_PARAMETERS + 2;
			}
			break;

			case SI5351_CLK2:
			{
				reg_addr = SI5351_MS2_PARAMETERS + 2;
			}
			break;

			default:
				return(true);
		}

		if(si5351_read_bulk(reg_addr, data, 1))
		{
			return(true);
		}
		
		reg_val = data[0];

		/* Clear the appropriate bits */
		reg_val &= ~(0x7c);

		if(div_by_4)
		{
			reg_val |= (SI5351_OUTPUT_CLK_DIVBY4);
		}
		else
		{
			reg_val &= ~(SI5351_OUTPUT_CLK_DIVBY4);
		}

		reg_val |= (r_div << SI5351_OUTPUT_CLK_DIV_SHIFT);

		data[0] = reg_val;
		return(si5351_write_bulk(reg_addr, data, 1));
	}
	
/*
 * si5351_set_CLK1_phase(void)
 *
 * Sets the clock phase.
 *  https://www.skyworksinc.com/-/media/Skyworks/SL/documents/public/application-notes/AN619.pdf
 * CLKx_PHOFF[4:0] = Round( DesiredOffset(sec) x 4 x Fvco)
 */
	EC si5351_set_CLK1_phase(uint8_t steps)
	{
		EC err = ERROR_CODE_NO_ERROR;
		uint8_t data[2];
		const uint8_t mask = 0x7F;
		
		if(steps > mask)
		{
			err = ERROR_CODE_SW_LOGIC_ERROR;
			steps = mask;
		}
		
		data[0] = steps & mask;
		if(si5351_write_bulk(SI5351_CLK1_PHASE_OFFSET, data, 1)) return ERROR_CODE_CLKGEN_NONRESPONSIVE;

		return err;
	}

uint8_t si5351_get_status()
{
	uint8_t reg_addr = SI5351_DEVICE_STATUS;
	uint8_t data[2];

	if(si5351_read_bulk(reg_addr, data, 1))
	{
		return(0);
	}
	
	return(data[0]);
}


#endif  /* #ifdef INCLUDE_SI5351_SUPPORT */
