OpenARDF/SignalSnagger/Software/AVR128DA48/SignalSnagger/include/atmel_start_pins.h

/*
 * Code generated from START.
 *
 * This file will be overwritten when reconfiguring your START project.
 * Please copy examples or other code you want to keep to a separate file
 * to avoid losing it when reconfiguring.
 */
#ifndef ATMEL_START_PINS_H_INCLUDED
#define ATMEL_START_PINS_H_INCLUDED

#define GREEN_PIN 4
#define RED_PIN 5

#include <port.h>

/************************************************************************************
PORTA Helper Functions
*************************************************************************************/

/**
 * \brief Set PA0 pull mode
 *
 * Configure pin to pull up, down or disable pull mode, supported pull
 * modes are defined by device used
 *
 * \param[in] pull_mode Pin pull mode
 */
static inline void PA0_set_pull_mode(const enum port_pull_mode pull_mode)
{
	PORTA_set_pin_pull_mode(0, pull_mode);
}

/**
 * \brief Set PA0 data direction
 *
 * Select if the pin data direction is input, output or disabled.
 * If disabled state is not possible, this function throws an assert.
 *
 * \param[in] direction PORT_DIR_IN  = Data direction in
 *                      PORT_DIR_OUT = Data direction out
 *                      PORT_DIR_OFF = Disables the pin
 *                      (low power state)
 */
static inline void PA0_set_dir(const enum port_dir dir)
{
	PORTA_set_pin_dir(0, dir);
}

/**
 * \brief Set PA0 input/sense configuration
 *
 * Enable/disable PA0 digital input buffer and pin change interrupt,
 * select pin interrupt edge/level sensing mode
 *
 * \param[in] isc PORT_ISC_INTDISABLE_gc    = Iterrupt disabled but input buffer enabled
 *                PORT_ISC_BOTHEDGES_gc     = Sense Both Edges
 *                PORT_ISC_RISING_gc        = Sense Rising Edge
 *                PORT_ISC_FALLING_gc       = Sense Falling Edge
 *                PORT_ISC_INPUT_DISABLE_gc = Digital Input Buffer disabled
 *                PORT_ISC_LEVEL_gc         = Sense low Level
 */
static inline void PA0_set_isc(const PORT_ISC_t isc)
{
	PORTA_pin_set_isc(0, isc);
}

/**
 * \brief Set PA0 inverted mode
 *
 * Enable or disable inverted I/O on a pin
 *
 * \param[in] inverted true  = I/O on PA0 is inverted
 *                     false = I/O on PA0 is not inverted
 */
static inline void PA0_set_inverted(const bool inverted)
{
	PORTA_pin_set_inverted(0, inverted);
}

/**
 * \brief Set PA0 level
 *
 * Sets output level on a pin
 *
 * \param[in] level true  = Pin level set to "high" state
 *                  false = Pin level set to "low" state
 */
static inline void PA0_set_level(const bool level)
{
	PORTA_set_pin_level(0, level);
}

/**
 * \brief Toggle output level on PA0
 *
 * Toggle the pin level
 */
static inline void PA0_toggle_level()
{
	PORTA_toggle_pin_level(0);
}

/**
 * \brief Get level on PA0
 *
 * Reads the level on a pin
 */
static inline bool PA0_get_level()
{
	return PORTA_get_pin_level(0);
}

/**
 * \brief Set PA1 pull mode
 *
 * Configure pin to pull up, down or disable pull mode, supported pull
 * modes are defined by device used
 *
 * \param[in] pull_mode Pin pull mode
 */
static inline void PA1_set_pull_mode(const enum port_pull_mode pull_mode)
{
	PORTA_set_pin_pull_mode(1, pull_mode);
}

/**
 * \brief Set PA1 data direction
 *
 * Select if the pin data direction is input, output or disabled.
 * If disabled state is not possible, this function throws an assert.
 *
 * \param[in] direction PORT_DIR_IN  = Data direction in
 *                      PORT_DIR_OUT = Data direction out
 *                      PORT_DIR_OFF = Disables the pin
 *                      (low power state)
 */
static inline void PA1_set_dir(const enum port_dir dir)
{
	PORTA_set_pin_dir(1, dir);
}

/**
 * \brief Set PA1 input/sense configuration
 *
 * Enable/disable PA1 digital input buffer and pin change interrupt,
 * select pin interrupt edge/level sensing mode
 *
 * \param[in] isc PORT_ISC_INTDISABLE_gc    = Iterrupt disabled but input buffer enabled
 *                PORT_ISC_BOTHEDGES_gc     = Sense Both Edges
 *                PORT_ISC_RISING_gc        = Sense Rising Edge
 *                PORT_ISC_FALLING_gc       = Sense Falling Edge
 *                PORT_ISC_INPUT_DISABLE_gc = Digital Input Buffer disabled
 *                PORT_ISC_LEVEL_gc         = Sense low Level
 */
static inline void PA1_set_isc(const PORT_ISC_t isc)
{
	PORTA_pin_set_isc(1, isc);
}

/**
 * \brief Set PA1 inverted mode
 *
 * Enable or disable inverted I/O on a pin
 *
 * \param[in] inverted true  = I/O on PA1 is inverted
 *                     false = I/O on PA1 is not inverted
 */
static inline void PA1_set_inverted(const bool inverted)
{
	PORTA_pin_set_inverted(1, inverted);
}

/**
 * \brief Set PA1 level
 *
 * Sets output level on a pin
 *
 * \param[in] level true  = Pin level set to "high" state
 *                  false = Pin level set to "low" state
 */
static inline void PA1_set_level(const bool level)
{
	PORTA_set_pin_level(1, level);
}

/**
 * \brief Toggle output level on PA1
 *
 * Toggle the pin level
 */
static inline void PA1_toggle_level()
{
	PORTA_toggle_pin_level(1);
}

/**
 * \brief Get level on PA1
 *
 * Reads the level on a pin
 */
static inline bool PA1_get_level()
{
	return PORTA_get_pin_level(1);
}


/************************************************************************************
PORTC Helper Functions
*************************************************************************************/

/**
 * \brief Set LED pull mode
 *
 * Configure pin to pull up, down or disable pull mode, supported pull
 * modes are defined by device used
 *
 * \param[in] pull_mode Pin pull mode
 */
static inline void LED_set_RED_pull_mode(const enum port_pull_mode pull_mode)
{
	PORTC_set_pin_pull_mode(RED_PIN, pull_mode);
}

/**
 * \brief Set red LED data direction
 *
 * Select if the pin data direction is input, output or disabled.
 * If disabled state is not possible, this function throws an assert.
 *
 * \param[in] direction PORT_DIR_IN  = Data direction in
 *                      PORT_DIR_OUT = Data direction out
 *                      PORT_DIR_OFF = Disables the pin
 *                      (low power state)
 */
static inline void LED_set_RED_dir(const enum port_dir dir)
{
	PORTC_set_pin_dir(RED_PIN, dir);
}

/**
 * \brief Set green LED data direction
 *
 * Select if the pin data direction is input, output or disabled.
 * If disabled state is not possible, this function throws an assert.
 *
 * \param[in] direction PORT_DIR_IN  = Data direction in
 *                      PORT_DIR_OUT = Data direction out
 *                      PORT_DIR_OFF = Disables the pin
 *                      (low power state)
 */
static inline void LED_set_GREEN_dir(const enum port_dir dir)
{
	PORTC_set_pin_dir(GREEN_PIN, dir);
}

/**
 * \brief Set LED input/sense configuration
 *
 * Enable/disable LED digital input buffer and pin change interrupt,
 * select pin interrupt edge/level sensing mode
 *
 * \param[in] isc PORT_ISC_INTDISABLE_gc    = Iterrupt disabled but input buffer enabled
 *                PORT_ISC_BOTHEDGES_gc     = Sense Both Edges
 *                PORT_ISC_RISING_gc        = Sense Rising Edge
 *                PORT_ISC_FALLING_gc       = Sense Falling Edge
 *                PORT_ISC_INPUT_DISABLE_gc = Digital Input Buffer disabled
 *                PORT_ISC_LEVEL_gc         = Sense low Level
 */
static inline void LED_set_RED_isc(const PORT_ISC_t isc)
{
	PORTC_pin_set_isc(RED_PIN, isc);
}

/**
 * \brief Set LED inverted mode
 *
 * Enable or disable inverted I/O on a pin
 *
 * \param[in] inverted true  = I/O on LED is inverted
 *                     false = I/O on LED is not inverted
 */
static inline void LED_set_RED_inverted(const bool inverted)
{
	PORTC_pin_set_inverted(RED_PIN, inverted);
}

/**
 * \brief Set red LED level
 *
 * Sets output level on a pin
 *
 * \param[in] level true  = Pin level set to "high" state
 *                  false = Pin level set to "low" state
 */
static inline void LED_set_RED_level(const bool level)
{
	PORTC_set_pin_level(RED_PIN, level); /* Low == LED off */
}

/**
 * \brief Set green LED level
 *
 * Sets output level on a pin
 *
 * \param[in] level true  = Pin level set to "high" state
 *                  false = Pin level set to "low" state
 */
static inline void LED_set_GREEN_level(const bool level)
{
	PORTC_set_pin_level(GREEN_PIN, level); /* Low == LED off */
}

/**
 * \brief Toggle output level on red LED
 *
 * Toggle the pin level
 */
static inline void LED_toggle_RED_level()
{
	PORTC_toggle_pin_level(RED_PIN);
}

/**
 * \brief Toggle output level on green LED
 *
 * Toggle the pin level
 */
static inline void LED_toggle_GREEN_level()
{
	PORTC_toggle_pin_level(GREEN_PIN);
}

/**
 * \brief Get level on LED
 *
 * Reads the level on a pin
 */
static inline bool LED_get_RED_level()
{
	return PORTC_get_pin_level(RED_PIN);
}

/**
 * \brief Set PC0 pull mode
 *
 * Configure pin to pull up, down or disable pull mode, supported pull
 * modes are defined by device used
 *
 * \param[in] pull_mode Pin pull mode
 */
static inline void PC0_set_pull_mode(const enum port_pull_mode pull_mode)
{
	PORTC_set_pin_pull_mode(0, pull_mode);
}

/**
 * \brief Set PC0 data direction
 *
 * Select if the pin data direction is input, output or disabled.
 * If disabled state is not possible, this function throws an assert.
 *
 * \param[in] direction PORT_DIR_IN  = Data direction in
 *                      PORT_DIR_OUT = Data direction out
 *                      PORT_DIR_OFF = Disables the pin
 *                      (low power state)
 */
static inline void PC0_set_dir(const enum port_dir dir)
{
	PORTC_set_pin_dir(0, dir);
}

/**
 * \brief Set PC0 input/sense configuration
 *
 * Enable/disable PC0 digital input buffer and pin change interrupt,
 * select pin interrupt edge/level sensing mode
 *
 * \param[in] isc PORT_ISC_INTDISABLE_gc    = Iterrupt disabled but input buffer enabled
 *                PORT_ISC_BOTHEDGES_gc     = Sense Both Edges
 *                PORT_ISC_RISING_gc        = Sense Rising Edge
 *                PORT_ISC_FALLING_gc       = Sense Falling Edge
 *                PORT_ISC_INPUT_DISABLE_gc = Digital Input Buffer disabled
 *                PORT_ISC_LEVEL_gc         = Sense low Level
 */
static inline void PC0_set_isc(const PORT_ISC_t isc)
{
	PORTC_pin_set_isc(0, isc);
}

/**
 * \brief Set PC0 inverted mode
 *
 * Enable or disable inverted I/O on a pin
 *
 * \param[in] inverted true  = I/O on PC0 is inverted
 *                     false = I/O on PC0 is not inverted
 */
static inline void PC0_set_inverted(const bool inverted)
{
	PORTC_pin_set_inverted(0, inverted);
}

/**
 * \brief Set PC0 level
 *
 * Sets output level on a pin
 *
 * \param[in] level true  = Pin level set to "high" state
 *                  false = Pin level set to "low" state
 */
static inline void PC0_set_level(const bool level)
{
	PORTC_set_pin_level(0, level);
}

/**
 * \brief Toggle output level on PC0
 *
 * Toggle the pin level
 */
static inline void PC0_toggle_level()
{
	PORTC_toggle_pin_level(0);
}

/**
 * \brief Get level on PC0
 *
 * Reads the level on a pin
 */
static inline bool PC0_get_level()
{
	return PORTC_get_pin_level(0);
}

/**
 * \brief Set PC1 pull mode
 *
 * Configure pin to pull up, down or disable pull mode, supported pull
 * modes are defined by device used
 *
 * \param[in] pull_mode Pin pull mode
 */
static inline void PC1_set_pull_mode(const enum port_pull_mode pull_mode)
{
	PORTC_set_pin_pull_mode(1, pull_mode);
}

/**
 * \brief Set PC1 data direction
 *
 * Select if the pin data direction is input, output or disabled.
 * If disabled state is not possible, this function throws an assert.
 *
 * \param[in] direction PORT_DIR_IN  = Data direction in
 *                      PORT_DIR_OUT = Data direction out
 *                      PORT_DIR_OFF = Disables the pin
 *                      (low power state)
 */
static inline void PC1_set_dir(const enum port_dir dir)
{
	PORTC_set_pin_dir(1, dir);
}

/**
 * \brief Set PC1 input/sense configuration
 *
 * Enable/disable PC1 digital input buffer and pin change interrupt,
 * select pin interrupt edge/level sensing mode
 *
 * \param[in] isc PORT_ISC_INTDISABLE_gc    = Iterrupt disabled but input buffer enabled
 *                PORT_ISC_BOTHEDGES_gc     = Sense Both Edges
 *                PORT_ISC_RISING_gc        = Sense Rising Edge
 *                PORT_ISC_FALLING_gc       = Sense Falling Edge
 *                PORT_ISC_INPUT_DISABLE_gc = Digital Input Buffer disabled
 *                PORT_ISC_LEVEL_gc         = Sense low Level
 */
static inline void PC1_set_isc(const PORT_ISC_t isc)
{
	PORTC_pin_set_isc(1, isc);
}

/**
 * \brief Set PC1 inverted mode
 *
 * Enable or disable inverted I/O on a pin
 *
 * \param[in] inverted true  = I/O on PC1 is inverted
 *                     false = I/O on PC1 is not inverted
 */
static inline void PC1_set_inverted(const bool inverted)
{
	PORTC_pin_set_inverted(1, inverted);
}

/**
 * \brief Set PC1 level
 *
 * Sets output level on a pin
 *
 * \param[in] level true  = Pin level set to "high" state
 *                  false = Pin level set to "low" state
 */
static inline void PC1_set_level(const bool level)
{
	PORTC_set_pin_level(1, level);
}

/**
 * \brief Toggle output level on PC1
 *
 * Toggle the pin level
 */
static inline void PC1_toggle_level()
{
	PORTC_toggle_pin_level(1);
}

/**
 * \brief Get level on PC1
 *
 * Reads the level on a pin
 */
static inline bool PC1_get_level()
{
	return PORTC_get_pin_level(1);
}




/************************************************************************************
PORTE Helper Functions
*************************************************************************************/

/**
 * \brief Set PE0 pull mode
 *
 * Configure pin to pull up, down or disable pull mode, supported pull
 * modes are defined by device used
 *
 * \param[in] pull_mode Pin pull mode
 */
static inline void PE0_set_pull_mode(const enum port_pull_mode pull_mode)
{
	PORTE_set_pin_pull_mode(0, pull_mode);
}

/**
 * \brief Set PE0 data direction
 *
 * Select if the pin data direction is input, output or disabled.
 * If disabled state is not possible, this function throws an assert.
 *
 * \param[in] direction PORT_DIR_IN  = Data direction in
 *                      PORT_DIR_OUT = Data direction out
 *                      PORT_DIR_OFF = Disables the pin
 *                      (low power state)
 */
static inline void PE0_set_dir(const enum port_dir dir)
{
	PORTE_set_pin_dir(0, dir);
}

/**
 * \brief Set PE0 input/sense configuration
 *
 * Enable/disable PE0 digital input buffer and pin change interrupt,
 * select pin interrupt edge/level sensing mode
 *
 * \param[in] isc PORT_ISC_INTDISABLE_gc    = Iterrupt disabled but input buffer enabled
 *                PORT_ISC_BOTHEDGES_gc     = Sense Both Edges
 *                PORT_ISC_RISING_gc        = Sense Rising Edge
 *                PORT_ISC_FALLING_gc       = Sense Falling Edge
 *                PORT_ISC_INPUT_DISABLE_gc = Digital Input Buffer disabled
 *                PORT_ISC_LEVEL_gc         = Sense low Level
 */
static inline void PE0_set_isc(const PORT_ISC_t isc)
{
	PORTE_pin_set_isc(0, isc);
}

/**
 * \brief Set PE0 inverted mode
 *
 * Enable or disable inverted I/O on a pin
 *
 * \param[in] inverted true  = I/O on PE0 is inverted
 *                     false = I/O on PE0 is not inverted
 */
static inline void PE0_set_inverted(const bool inverted)
{
	PORTE_pin_set_inverted(0, inverted);
}

/**
 * \brief Set PE0 level
 *
 * Sets output level on a pin
 *
 * \param[in] level true  = Pin level set to "high" state
 *                  false = Pin level set to "low" state
 */
static inline void PE0_set_level(const bool level)
{
	PORTE_set_pin_level(0, level);
}

/**
 * \brief Toggle output level on PE0
 *
 * Toggle the pin level
 */
static inline void PE0_toggle_level()
{
	PORTE_toggle_pin_level(0);
}

/**
 * \brief Get level on PE0
 *
 * Reads the level on a pin
 */
static inline bool PE0_get_level()
{
	return PORTE_get_pin_level(0);
}

/**
 * \brief Set PE1 pull mode
 *
 * Configure pin to pull up, down or disable pull mode, supported pull
 * modes are defined by device used
 *
 * \param[in] pull_mode Pin pull mode
 */
static inline void PE1_set_pull_mode(const enum port_pull_mode pull_mode)
{
	PORTE_set_pin_pull_mode(1, pull_mode);
}

/**
 * \brief Set PE1 data direction
 *
 * Select if the pin data direction is input, output or disabled.
 * If disabled state is not possible, this function throws an assert.
 *
 * \param[in] direction PORT_DIR_IN  = Data direction in
 *                      PORT_DIR_OUT = Data direction out
 *                      PORT_DIR_OFF = Disables the pin
 *                      (low power state)
 */
static inline void PE1_set_dir(const enum port_dir dir)
{
	PORTE_set_pin_dir(1, dir);
}

/**
 * \brief Set PE1 input/sense configuration
 *
 * Enable/disable PE1 digital input buffer and pin change interrupt,
 * select pin interrupt edge/level sensing mode
 *
 * \param[in] isc PORT_ISC_INTDISABLE_gc    = Iterrupt disabled but input buffer enabled
 *                PORT_ISC_BOTHEDGES_gc     = Sense Both Edges
 *                PORT_ISC_RISING_gc        = Sense Rising Edge
 *                PORT_ISC_FALLING_gc       = Sense Falling Edge
 *                PORT_ISC_INPUT_DISABLE_gc = Digital Input Buffer disabled
 *                PORT_ISC_LEVEL_gc         = Sense low Level
 */
static inline void PE1_set_isc(const PORT_ISC_t isc)
{
	PORTE_pin_set_isc(1, isc);
}

/**
 * \brief Set PE1 inverted mode
 *
 * Enable or disable inverted I/O on a pin
 *
 * \param[in] inverted true  = I/O on PE1 is inverted
 *                     false = I/O on PE1 is not inverted
 */
static inline void PE1_set_inverted(const bool inverted)
{
	PORTE_pin_set_inverted(1, inverted);
}

/**
 * \brief Set PE1 level
 *
 * Sets output level on a pin
 *
 * \param[in] level true  = Pin level set to "high" state
 *                  false = Pin level set to "low" state
 */
static inline void PE1_set_level(const bool level)
{
	PORTE_set_pin_level(1, level);
}

/**
 * \brief Toggle output level on PE1
 *
 * Toggle the pin level
 */
static inline void PE1_toggle_level()
{
	PORTE_toggle_pin_level(1);
}

/**
 * \brief Get level on PE1
 *
 * Reads the level on a pin
 */
static inline bool PE1_get_level()
{
	return PORTE_get_pin_level(1);
}


#endif /* ATMEL_START_PINS_H_INCLUDED */
