OpenARDF/SignalSnagger/Software/AVR128DA48/SignalSnagger/include/eeprommanager.h

/*
 *  MIT License
 *
 *  Copyright (c) 2021 DigitalConfections
 *
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
 *  THE SOFTWARE IS PROVIDED "AS IS", WITHOUT WARRANTY OF ANY KIND, EXPRESS OR
 *  IMPLIED, INCLUDING BUT NOT LIMITED TO THE WARRANTIES OF MERCHANTABILITY,
 *  FITNESS FOR A PARTICULAR PURPOSE AND NONINFRINGEMENT. IN NO EVENT SHALL THE
 *  AUTHORS OR COPYRIGHT HOLDERS BE LIABLE FOR ANY CLAIM, DAMAGES OR OTHER
 *  LIABILITY, WHETHER IN AN ACTION OF CONTRACT, TORT OR OTHERWISE, ARISING FROM,
 *  OUT OF OR IN CONNECTION WITH THE SOFTWARE OR THE USE OR OTHER DEALINGS IN THE
 *  SOFTWARE.
 */

#ifndef __EEPROMMANAGER_H__
#define __EEPROMMANAGER_H__

#include "defs.h"

#ifdef ATMEL_STUDIO_7
#include <avr/eeprom.h>
#endif  /* ATMEL_STUDIO_7 */

#include <time.h>
#include <avr/eeprom.h>

#define GUARDSIZE sizeof(uint32_t)

struct EE_prom
{
	uint16_t eeprom_initialization_flag;
	uint32_t guard4_1;
	time_t event_start_epoch; 
	uint32_t guard4_2;
	time_t event_finish_epoch; 
	uint32_t guard4_3;
 	char pattern_text[MAX_PATTERN_TEXT_LENGTH + 2]; 
	uint32_t guard4_4;
	char foxoring_pattern_text[MAX_PATTERN_TEXT_LENGTH + 2]; 
	uint32_t guard4_5;
 	char stationID_text[MAX_PATTERN_TEXT_LENGTH + 2]; 
	uint32_t guard4_6;
	uint8_t unlockCode[MAX_UNLOCK_CODE_LENGTH + 2];
	uint32_t guard4_7;
	Fox_t fox_setting_none;
	uint32_t guard4_8;
	Fox_t fox_setting_classic;
	uint32_t guard4_9;
	Fox_t fox_setting_sprint;
	uint32_t guard4_10;
	Fox_t fox_setting_foxoring;
	uint32_t guard4_11;
	Fox_t fox_setting_blind;
	uint32_t guard4_12;
	uint8_t utc_offset; 
	uint32_t guard4_13;
	Frequency_Hz rtty_offset; 
	uint32_t guard4_14;
	uint16_t rf_power;
	uint32_t guard4_15;
	uint8_t id_codespeed;
	uint32_t guard4_16;
	uint8_t pattern_codespeed;
	uint32_t guard4_17;
	uint8_t foxoring_pattern_codespeed;
	uint32_t guard4_18;
	int16_t off_air_seconds; 
	uint32_t guard4_19;
	int16_t on_air_seconds; 
	uint32_t guard4_20;
	int16_t ID_period_seconds; 
	uint32_t guard4_21;
	int16_t intra_cycle_delay_time; 
	uint32_t guard4_22;
	Event_t event_setting; 
	uint32_t guard4_23;
	uint32_t frequency;
	uint32_t guard4_24;
	uint32_t frequency_low;
	uint32_t guard4_25;
	uint32_t frequency_med; 
	uint32_t guard4_26;
	uint32_t frequency_high;
	uint32_t guard4_27;
	uint32_t frequency_beacon;
	uint32_t guard4_28;
	bool master_setting;
	uint32_t guard4_29;
	float voltage_threshold;
	uint32_t guard4_30;
	uint16_t clock_calibration;
	uint32_t guard4_31;
	uint8_t days_to_run;
	uint32_t guard4_32;
	uint16_t i2c_failure_count;
	Frequency_Hz channel_frequency[NUMBER_OF_FREQUENCY_CHANNELS];
	uint8_t channel_name[NUMBER_OF_FREQUENCY_CHANNELS];
	FrequencyMode_t frequency_mode;
	BatteryCapacity_t battery_capacity;
	uint8_t battery_threshold;
	uint8_t active_memory;

};

typedef enum
{
	Eeprom_initialization_flag = 0, /* 2 bytes */
	Guard4_1 = Eeprom_initialization_flag + sizeof(uint16_t),		/**** Guard = 4 bytes ****/
	Event_start_epoch = Guard4_1 + GUARDSIZE, /* 4 bytes */
	Guard4_2 = Event_start_epoch + sizeof(time_t),					/**** Guard = 4 bytes ****/
	Event_finish_epoch =  Guard4_2 + GUARDSIZE, /* 4 bytes */
	Guard4_3 = Event_finish_epoch + sizeof(time_t),					/**** Guard = 4 bytes ****/
	Pattern_text =  Guard4_3 + GUARDSIZE, /* MAX_PATTERN_TEXT_LENGTH + 1  bytes */
	Guard4_4 = Pattern_text + MAX_PATTERN_TEXT_LENGTH+2,			/**** Guard = 4 bytes ****/
	Foxoring_pattern_text =  Guard4_4 + GUARDSIZE,  /* MAX_PATTERN_TEXT_LENGTH + 1 bytes */
	Guard4_5 = Foxoring_pattern_text + MAX_PATTERN_TEXT_LENGTH+2,	/**** Guard = 4 bytes ****/
	StationID_text =  Guard4_5 + GUARDSIZE, /* MAX_PATTERN_TEXT_LENGTH + 1 bytes */
	Guard4_6 = StationID_text + MAX_PATTERN_TEXT_LENGTH+2,		/**** Guard = 4 bytes ****/
	UnlockCode =  Guard4_6 + GUARDSIZE, /* UNLOCK_CODE_SIZE + 2 bytes */
	Guard4_7 = UnlockCode + UNLOCK_CODE_SIZE+2,					/**** Guard = 4 bytes ****/
	Fox_setting_none =  Guard4_7 + GUARDSIZE, /* 1 bytes */
	Guard4_8 = Fox_setting_none + sizeof(Fox_t),					/**** Guard = 4 bytes ****/
	Fox_setting_classic =  Guard4_8 + GUARDSIZE, /* 1 bytes */
	Guard4_9 = Fox_setting_classic + sizeof(Fox_t),					/**** Guard = 4 bytes ****/
	Fox_setting_sprint =  Guard4_9 + GUARDSIZE, /* 1 bytes */
	Guard4_10 = Fox_setting_sprint + sizeof(Fox_t),					/**** Guard = 4 bytes ****/
	Fox_setting_foxoring =  Guard4_10 + GUARDSIZE, /* 1 bytes */
	Guard4_11 = Fox_setting_foxoring + sizeof(Fox_t),				/**** Guard = 4 bytes ****/
	Fox_setting_blind =  Guard4_11 + GUARDSIZE, /* 1 bytes */
	Guard4_12 = Fox_setting_blind + sizeof(Fox_t),					/**** Guard = 4 bytes ****/
	Utc_offset =  Guard4_12 + GUARDSIZE, /* 1 byte */
	Guard4_13 = Utc_offset + sizeof(uint8_t),						/**** Guard = 4 bytes ****/
	RTTY_offset =  Guard4_13 + GUARDSIZE, /* 4 bytes */
	Guard4_14 = RTTY_offset + sizeof(Frequency_Hz),					/**** Guard = 4 bytes ****/
	RF_Power =  Guard4_14 + GUARDSIZE, /* 2 bytes */
	Guard4_15 = RF_Power + sizeof(int16_t),							/**** Guard = 4 bytes ****/
	Id_codespeed =  Guard4_15 + GUARDSIZE, /* 1 byte */
	Guard4_16 = Id_codespeed + sizeof(uint8_t),						/**** Guard = 4 bytes ****/
	Pattern_Code_Speed =  Guard4_16 + GUARDSIZE, /* 1 byte */
	Guard4_17 = Pattern_Code_Speed + sizeof(uint8_t),				/**** Guard = 4 bytes ****/
	Foxoring_Pattern_Code_Speed =  Guard4_17 + GUARDSIZE, /* 1 byte */
	Guard4_18 = Foxoring_Pattern_Code_Speed + sizeof(uint8_t),		/**** Guard = 4 bytes ****/
	Off_Air_Seconds =  Guard4_18 + GUARDSIZE, /* 2 bytes */
	Guard4_19 = Off_Air_Seconds + sizeof(int16_t),					/**** Guard = 4 bytes ****/
	On_Air_Seconds =  Guard4_19 + GUARDSIZE, /* 2 bytes */
	Guard4_20 = On_Air_Seconds + sizeof(int16_t),					/**** Guard = 4 bytes ****/
	ID_Period_Seconds =  Guard4_20 + GUARDSIZE, /* 2 bytes */
	Guard4_21 = ID_Period_Seconds + sizeof(int16_t),				/**** Guard = 4 bytes ****/
	Intra_Cycle_Delay_Seconds =  Guard4_21 + GUARDSIZE, /* 2 bytes */
	Guard4_22 = Intra_Cycle_Delay_Seconds + sizeof(int16_t),		/**** Guard = 4 bytes ****/
	Event_setting =  Guard4_22 + GUARDSIZE, /* 1 byte */ 
	Guard4_23 = Event_setting + sizeof(Event_t),					/**** Guard = 4 bytes ****/
	Frequency =  Guard4_23 + GUARDSIZE,  /* 4 bytes */
	Guard4_24 = Frequency + sizeof(Frequency_Hz),					/**** Guard = 4 bytes ****/
	Frequency_Low =  Guard4_24 + GUARDSIZE,  /* 4 bytes */
	Guard4_25 = Frequency_Low + sizeof(Frequency_Hz),				/**** Guard = 4 bytes ****/
	Frequency_Med =  Guard4_25 + GUARDSIZE,  /* 4 bytes */
	Guard4_26 = Frequency_Med + sizeof(Frequency_Hz),				/**** Guard = 4 bytes ****/
	Frequency_Hi =  Guard4_26 + GUARDSIZE,  /* 4 bytes */
	Guard4_27 = Frequency_Hi + sizeof(Frequency_Hz),				/**** Guard = 4 bytes ****/
	Frequency_Beacon =  Guard4_27 + GUARDSIZE,  /* 4 bytes */
	Guard4_28 = Frequency_Beacon + sizeof(Frequency_Hz),			/**** Guard = 4 bytes ****/
	Master_setting =  Guard4_28 + GUARDSIZE, /* bool: 1 byte */ 
	Guard4_29 = Master_setting + sizeof(bool),						/**** Guard = 4 bytes ****/
	Voltage_threshold =  Guard4_29 + GUARDSIZE,   /* 4 bytes */
	Guard4_30 = Voltage_threshold + sizeof(float),					/**** Guard = 4 bytes ****/
	Clock_calibration =  Guard4_30 + GUARDSIZE,   /* 2 bytes */
	Guard4_31 = Clock_calibration + sizeof(uint16_t),				/**** Guard = 2 bytes ****/
	Days_to_run = Guard4_31 + GUARDSIZE,   /* 1 byte */
	Guard4_32 = Days_to_run + sizeof(uint8_t),	                    /**** Guard = 2 bytes ****/
	I2C_failure_count = Guard4_32 + GUARDSIZE,   /* 2 bytes */
	Frequency_Memory = I2C_failure_count + sizeof(uint16_t),
	Channel_Name =  Frequency_Memory + NUMBER_OF_FREQUENCY_CHANNELS * sizeof(Frequency_Hz),
	Frequency_Mode = Channel_Name + NUMBER_OF_FREQUENCY_CHANNELS * sizeof(uint8_t),
	Battery_Capacity = Frequency_Mode + sizeof(uint8_t),
	Battery_Threshold = Battery_Capacity + sizeof(uint8_t),
	Active_Memory = Battery_Threshold + sizeof(uint8_t)
} EE_var_t;


class EepromManager
{
	/*variables */
	public:
	protected:
	private:

	/*functions */
	public:
	EepromManager();
	~EepromManager();

	static const struct EE_prom ee_vars;

	bool initializeEEPROMVars(void);
	bool readNonVols(void);
	void updateEEPROMVar(EE_var_t v, void* val);
	void saveAllEEPROM();

	protected:
	private:
	EepromManager( const EepromManager &c );
	EepromManager& operator=( const EepromManager &c );
};  /*EepromManager */

#endif  /*__EEPROMMANAGER_H__ */
