OpenARDF/SignalSnagger/Software/AVR128DA48/SignalSnagger/src/tca.cpp

/*
 *  MIT License
 *
 *  Copyright (c) 2022 DigitalConfections
 *
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
 *  THE SOFTWARE IS PROVIDED "AS IS", WITHOUT WARRANTY OF ANY KIND, EXPRESS OR
 *  IMPLIED, INCLUDING BUT NOT LIMITED TO THE WARRANTIES OF MERCHANTABILITY,
 *  FITNESS FOR A PARTICULAR PURPOSE AND NONINFRINGEMENT. IN NO EVENT SHALL THE
 *  AUTHORS OR COPYRIGHT HOLDERS BE LIABLE FOR ANY CLAIM, DAMAGES OR OTHER
 *  LIABILITY, WHETHER IN AN ACTION OF CONTRACT, TORT OR OTHERWISE, ARISING FROM,
 *  OUT OF OR IN CONNECTION WITH THE SOFTWARE OR THE USE OR OTHER DEALINGS IN THE
 *  SOFTWARE.
 */

/*
 * tca.cpp
 *
 * Created: 5/18/2024 11:14:15 AM
 */ 

#include "defs.h"
#include "tca.h"

#include "port.h"
#include "binio.h"

uint8_t g_pwm_setting = 0;

void TIMERA_init(void)
{
	/********************************************************************************/
	/**
	Single-Slope PWM Generation
	For single-slope Pulse-Width Modulation (PWM) generation the period (T) is controlled by the TCAn.PER register,
	while the values of the TCAn.CMPn registers control the duty cycles of the generated waveforms. The waveform generator
	output is set at BOTTOM and cleared on the compare match between the TCAn.CNT and TCAn.CMPn registers.
	CMPn = BOTTOM will produce a static low signal on WOn while CMPn > TOP will produce a static high signal on
	WOn.
	*/
	
	PORTE_set_pin_dir(PWM, PORT_DIR_OUT); /* PE2 */
	PORTE_set_pin_dir(3, PORT_DIR_IN);
	PORTE_set_pin_pull_mode(3, PORT_PULL_OFF);
	
	TCA0.SINGLE.PER = 0x2580; /* Set timer period to 2.5 kHz */
	PORTMUX.TCAROUTEA = PORTMUX_TCA0_PORTE_gc; /* PWM WO2 out on PE2 */
	TCA0.SINGLE.CTRLB = TCA_SINGLE_CMP2EN_bm | TCA_SINGLE_WGMODE_SINGLESLOPE_gc; /* Set waveform generation mode single-slope, and enable compare channel */
	setPWM(MAX_PWM_SETTING/2); /* Start at 50% duty cycle */
	TCA0.SINGLE.CTRLA |= TCA_SINGLE_ENABLE_bm; /* enable TimerA0 */
}

//const uint16_t rf_gain_settings[MAX_PWM_SETTING+1] = {0, 960, 1920, 2880, 3840, 4800, 5760, 6720, 7680, 8640, 9600}; /* 2500 Hz PWM period */
const uint16_t rf_gain_settings[MAX_PWM_SETTING+1] = {0, 672, 1344, 2016, 2688, 3360, 4032, 4704, 5376, 6048, 6720}; /* 2500 Hz PWM period */

void setPWM(uint8_t duty)
{
	uint8_t dc = CLAMP((uint8_t)0, duty, MAX_PWM_SETTING);
	
#ifdef TCA0_USE_SPLIT
	uint16_t newCMP = (((uint16_t)(TCA0.SPLIT.HPER) * dc) / MAX_PWM_SETTING);
	TCA0.SPLIT.HCMP0 = (uint8_t)newCMP;
#else
// 	uint32_t newCMP = (((uint32_t)(TCA0.SINGLE.PER) * dc) / MAX_PWM_SETTING);
// 	TCA0.SINGLE.CMP2 = (uint16_t)newCMP;
	TCA0.SINGLE.CMP2 = rf_gain_settings[dc];
#endif

	g_pwm_setting = dc;
}

uint8_t getPWM(void)
{
	return(g_pwm_setting);
}
