OpenARDF/SignalSnagger/Software/AVR128DA48/SignalSnagger/src/util.cpp

/*
 *  MIT License
 *
 *  Copyright (c) 2022 DigitalConfections
 *
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
 *  THE SOFTWARE IS PROVIDED "AS IS", WITHOUT WARRANTY OF ANY KIND, EXPRESS OR
 *  IMPLIED, INCLUDING BUT NOT LIMITED TO THE WARRANTIES OF MERCHANTABILITY,
 *  FITNESS FOR A PARTICULAR PURPOSE AND NONINFRINGEMENT. IN NO EVENT SHALL THE
 *  AUTHORS OR COPYRIGHT HOLDERS BE LIABLE FOR ANY CLAIM, DAMAGES OR OTHER
 *  LIABILITY, WHETHER IN AN ACTION OF CONTRACT, TORT OR OTHERWISE, ARISING FROM,
 *  OUT OF OR IN CONNECTION WITH THE SOFTWARE OR THE USE OR OTHER DEALINGS IN THE
 *  SOFTWARE.
 */


#include "util.h"
#include <avr/eeprom.h>
#include <stdio.h>
#include <stdlib.h>
#include <string.h>
#include <ctype.h>
#include <math.h>

/**
 * Returns a-b
 * It appears difftime might not be handling subtraction of unsigned arguments correctly with current compiler. This function avoids any problems.
 */
int32_t timeDif(time_t a, time_t b)
{
	int32_t dif; // = difftime(now, g_event_start_epoch); // returns arg1 - arg2
	if(a > b)
		dif = a - b;
	else
		dif = -(b - a);

	return dif;
}


/***********************************************************************************************
 *  Print Formatting Utility Functions
 ************************************************************************************************/

#ifdef DATE_STRING_SUPPORT_ENABLED

/**
 * Returns parsed time structure from a string of format "yyyy-mm-ddThh:mm:ssZ"
 */
bool mystrptime(char* s, struct tm* ltm) {
  const int month_days[12] = {31, 28, 31, 30, 31, 30, 31, 31, 30, 31, 30, 31};
  char temp[6];
  char str[21];
  int hold;
  bool isleap;
  char *ptr0;
  char *ptr1;
  bool noSeconds = false;

  strncpy(str, s, 21);  // "yyyy-mm-ddThh:mm:ssZ\0" <- maximum length null-terminated string

  ptr1 = strchr(str, 'Z');
  if(ptr1) *ptr1 = '\0'; // erase the 'Z' character at the end if one exists

  noSeconds = (strlen(str) < 17);

  ptr1 = strchr(str, '-');
  *ptr1 = '\0';
  strncpy(temp, str, 5);
  ++ptr1;
  hold = atoi(temp);
  isleap = is_leap_year(hold);
  hold -= 1900;
  if((hold < 0) || (hold > 200)) return true;
  ltm->tm_year = hold;

  ptr0 = ptr1;

  ptr1 = strchr(ptr0, '-');
  *ptr1 = '\0';
  strncpy(temp, ptr0, 3);
  ++ptr1;
  hold = atoi(temp) - 1;
  if((hold > 11) || (hold < 0)) return true;
  ltm->tm_mon = hold;

  ptr0 = ptr1;

  ptr1 = strchr(ptr0, 'T');
  *ptr1 = '\0';
  strncpy(temp, ptr0, 3);
  ++ptr1;
  hold = atoi(temp);
  if((hold > 31) || (hold < 1)) return true;
  ltm->tm_mday = hold;

  ptr0 = ptr1;

  ltm->tm_yday = 0;
  for(int i=0; i<ltm->tm_mon; i++)
  {
    ltm->tm_yday += month_days[i];
    if((i==1) && isleap) ltm->tm_yday++;
  }

  ltm->tm_yday += (ltm->tm_mday - 1);

  ptr1 = strchr(ptr0, ':');
  *ptr1 = '\0';
  strncpy(temp, ptr0, 3);
  ++ptr1;
  hold = atoi(temp);
  if((hold > 23) || (hold < 0)) return true;
  ltm->tm_hour = hold;

  ptr0 = ptr1;

  if(noSeconds)
  {
	  strncpy(temp, ptr0, 3);
	  hold = atoi(temp);
	  if(hold > 59) return true;
	  ltm->tm_min = hold;
  }
  else
  {
	  ptr1 = strchr(ptr0, ':');
	  *ptr1 = '\0';
	  strncpy(temp, ptr0, 3);
	  ++ptr1;
	  hold = atoi(temp);
	  if(hold > 59) return true;
	  ltm->tm_min = hold;

	  hold = atoi(ptr1);
	  if(hold > 59) return true;
	  ltm->tm_sec = hold;
  }

  return false;
}


/**
 * Converts a string of format "yyyy-mm-ddThh:mm:ss" to seconds since 1900
 */
uint32_t convertTimeStringToEpoch(char * s)
{
  unsigned long result = 0;
  struct tm ltm = {0};

  if (!mystrptime(s, &ltm)) {
    result = ltm.tm_sec + ltm.tm_min*60 + ltm.tm_hour*3600L + ltm.tm_yday*86400L +
    (ltm.tm_year-70)*31536000L + ((ltm.tm_year-69)/4)*86400L -
    ((ltm.tm_year-1)/100)*86400L + ((ltm.tm_year+299)/400)*86400L;
  }

  return result;
}

#endif //  DATE_STRING_SUPPORT_ENABLED

/** 
 * Checks a string to see if it contains only numerical characters
 */
bool only_digits(char *s)
{
	while(*s)
	{
		if(isdigit(*s++) == 0)
		{
			return( false);
		}
	}

	return( true);
}

/** 
 * Checks a string to see if it contains only alphanumerical characters
 */
bool isDisplayable(char *s, int max)
{
	int i = max;
	
	while(*s && i--)
	{
		if((*s < 32) && (*s > 126))
		{
			return( false);
		}
	}

	return( true);
}


/** 
 * Convert a frequency string to a proper Hz value and string format based on assumptions 
 * related to the size and decimal properties of the number contained in the string.
 * result = pointer to a character sting to hold the frequency string
 * freq = the frequency value to be represented as a string
 * Returns 1 if an error is detected
 */
bool frequencyString(char* result, uint32_t freq)
{
	bool failure = true;
	
	if(!result)
	{
		return(failure);
	}
	
	if((freq > 3200000) && (freq < 8000000)) // Accept only a Hz value to be expressed in kHz
	{
//		uint32_t k = (freq % 1000000) / 1000;
		uint32_t c = (freq % 1000);
//		sprintf(result, "%lu.%03lu.%03lu", freq/1000000, k, c);
		sprintf(result, "%lu.%1lu", freq/1000, c/100);
		
		failure = false;
	}
	
	return(failure);	
}

/** 
 * Convert a frequency string to a proper Hz value and string format based on assumptions 
 * related to the size and decimal properties of the number contained in the string.
 * str = pointer to a string containing the frequency string
 * result = pointer to a Frequency_Hz variable to hold the frequency in Hz
 * Returns 1 if an error is detected
 */
bool frequencyVal(char* str, Frequency_Hz* result)
{
	bool failure = true;
	
	if(!str)
	{
		return(failure);
	}
	
	int decimal = '.';
	char* decimalLocation = strchr(str, decimal);
	Frequency_Hz temp;
	
	if(decimalLocation) // Assume Hz or kHz
	{
		float f = atof(str);
		
		if((f > 3.5) && (f < 4.0))
		{
			f *= 1000000.;
			failure = false;
		}
		else if((f > 3500.) && (f < 4000.))
		{
			f *= 1000.;
			failure = false;
		}
		else if((f > 3500000.) && (f < 4000000.))
		{
			failure = false;
		}
		
		if(!failure)
		{
			temp = (Frequency_Hz)ceilf(f);
			temp = temp - (temp % 100);
			if(result) *result = temp;
			sprintf(str, "%4.1f kHz", (double)f);
		}
	}
	else
	{
		Frequency_Hz f = (Frequency_Hz)atol(str);
		
		if((f > 3500) && (f < 4000))
		{
			f *= 1000;
			failure = false;
		}
		else if((f > 3500000) && (f < 4000000))
		{
			f = f - (f % 100);
			failure = false;
		}
		
		if(!failure)
		{
			if(result) *result = f;
			sprintf(str, "%lu.%1lu kHz", f/1000, (f % 1000)/100);
		}
	}
	
	return(failure);	
}
